jkobler/tricorder-GUI/resources/3D Models/01. TOS Tricorder(Empty)-STL Files/C.jpg

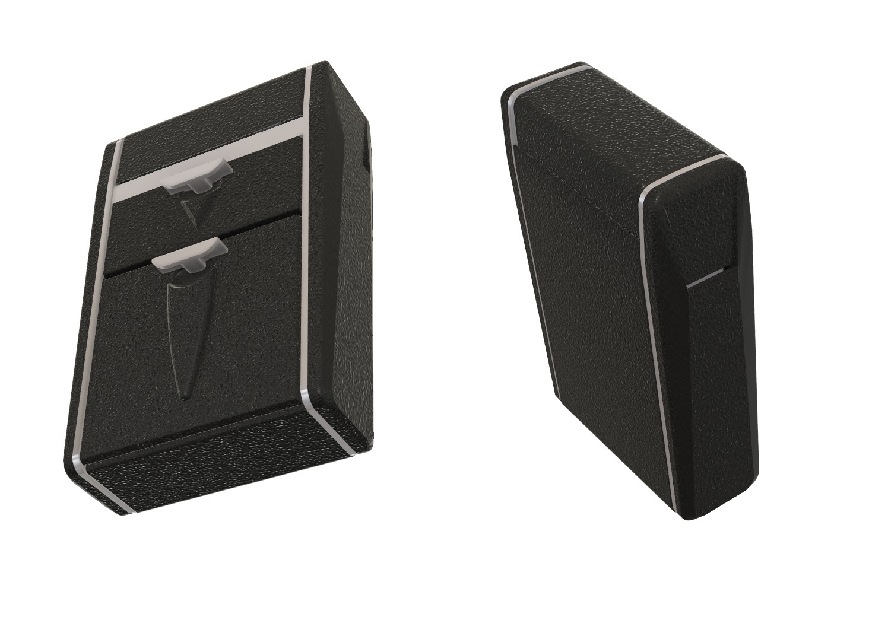
resources/3D Models/01. TOS Tricorder(Empty)-STL Files/C.jpg
