jkobler/tricorder-GUI/resources/3D Models/01. TOS Tricorder(Empty)-STL Files/L.jpg

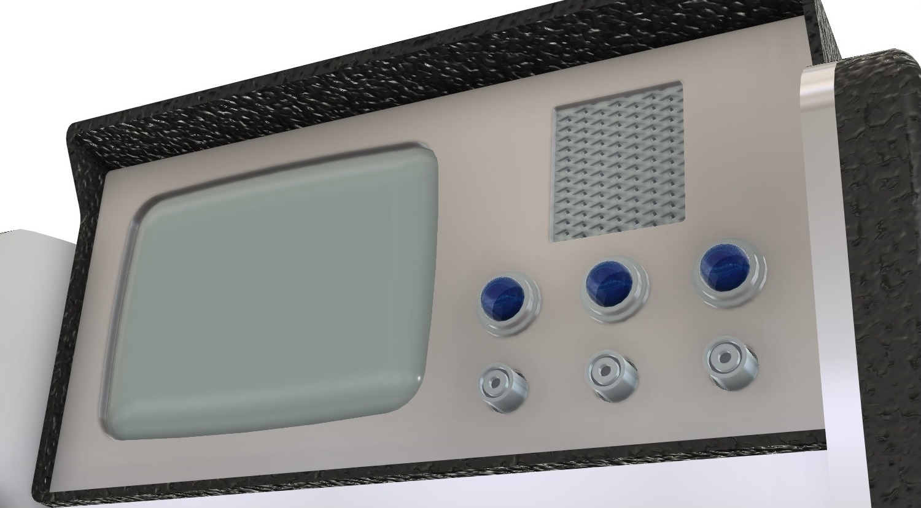
resources/3D Models/01. TOS Tricorder(Empty)-STL Files/L.jpg
