jkobler/tricorder-GUI/resources/3D Models/01. TOS Tricorder(Empty)-STL Files/M.jpg

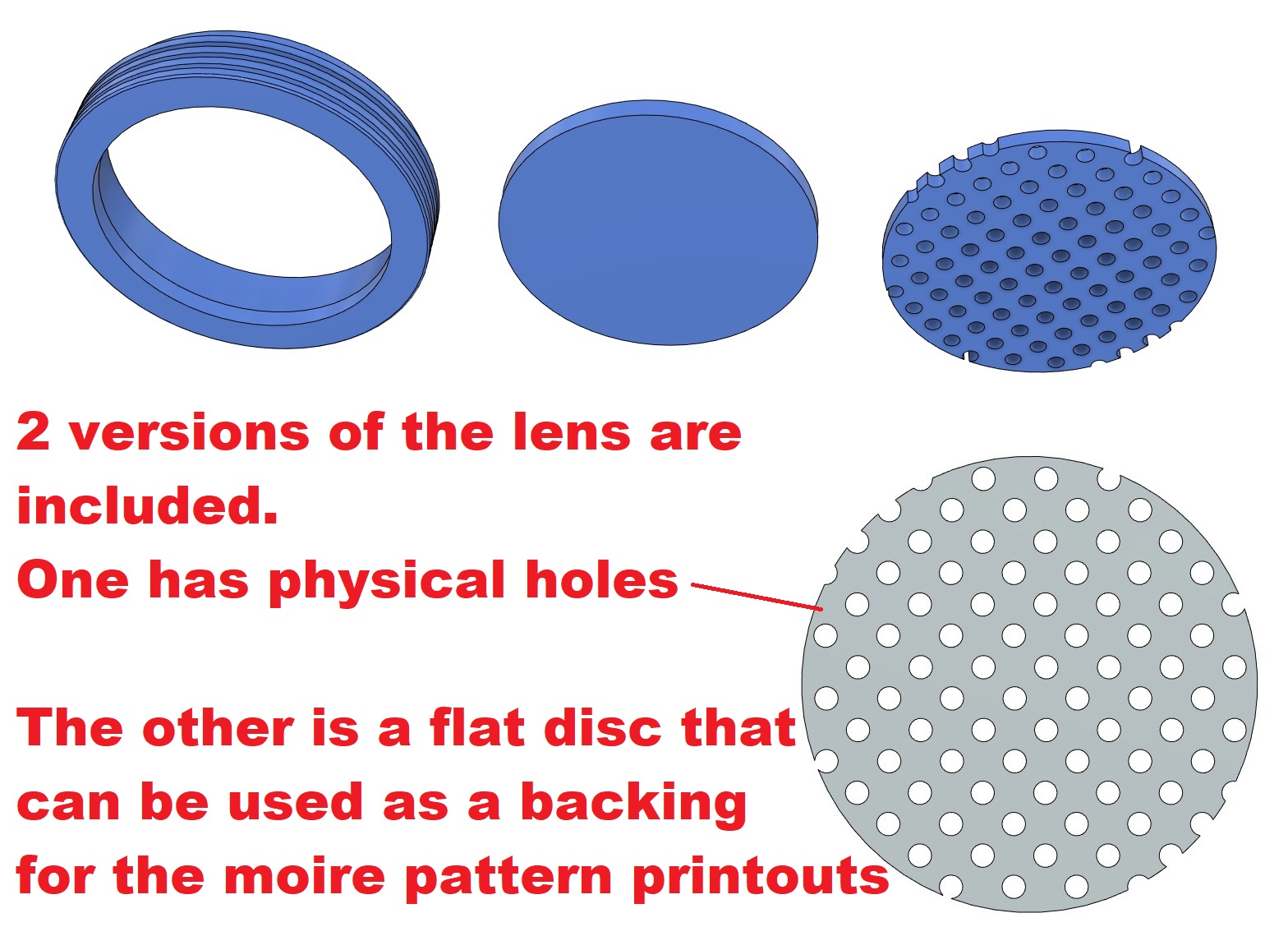
resources/3D Models/01. TOS Tricorder(Empty)-STL Files/M.jpg
