jkobler/tricorder-GUI/resources/3D Models/01. TOS Tricorder(Empty)-STL Files/Matts P1 - side view - internal sketch 1 - drawing 2.2.B-(C)Z.png

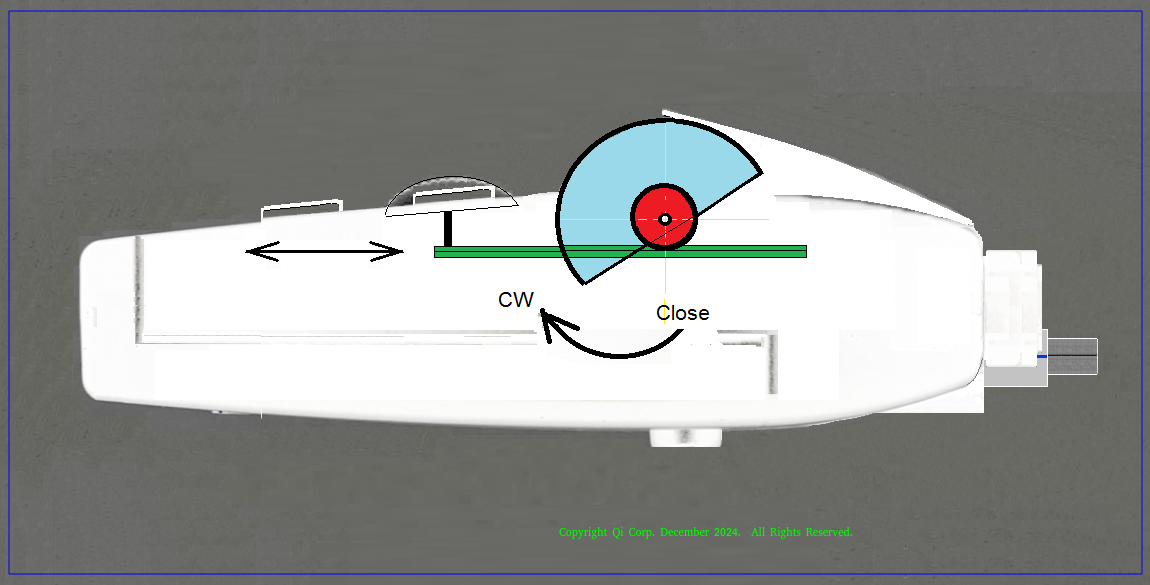
resources/3D Models/01. TOS Tricorder(Empty)-STL Files/Matts P1 - side view - internal sketch 1 - drawing 2.2.B-(C)Z.png
