jkobler/tricorder-GUI/resources/3D Models/01. TOS Tricorder(Empty)-STL Files/X.jpg

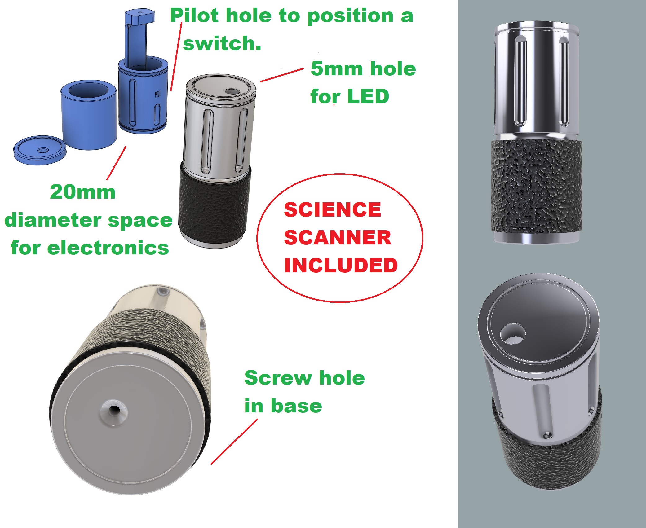
resources/3D Models/01. TOS Tricorder(Empty)-STL Files/X.jpg
