jkobler/tricorder-GUI/resources/images/2.0 TFT Display Block.JPG

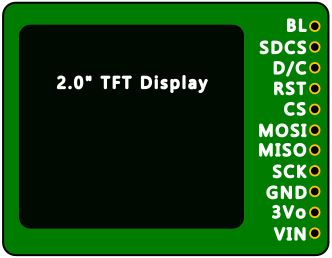
resources/images/2.0 TFT Display Block.JPG
