jkobler/tricorder-GUI/resources/images/Feather ESP32-S2 Block.JPG

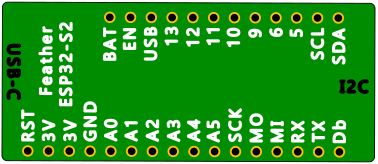
resources/images/Feather ESP32-S2 Block.JPG
