jkobler/tricorder-GUI/resources/images/Moire/Moire1200-BetaBottom.jpg

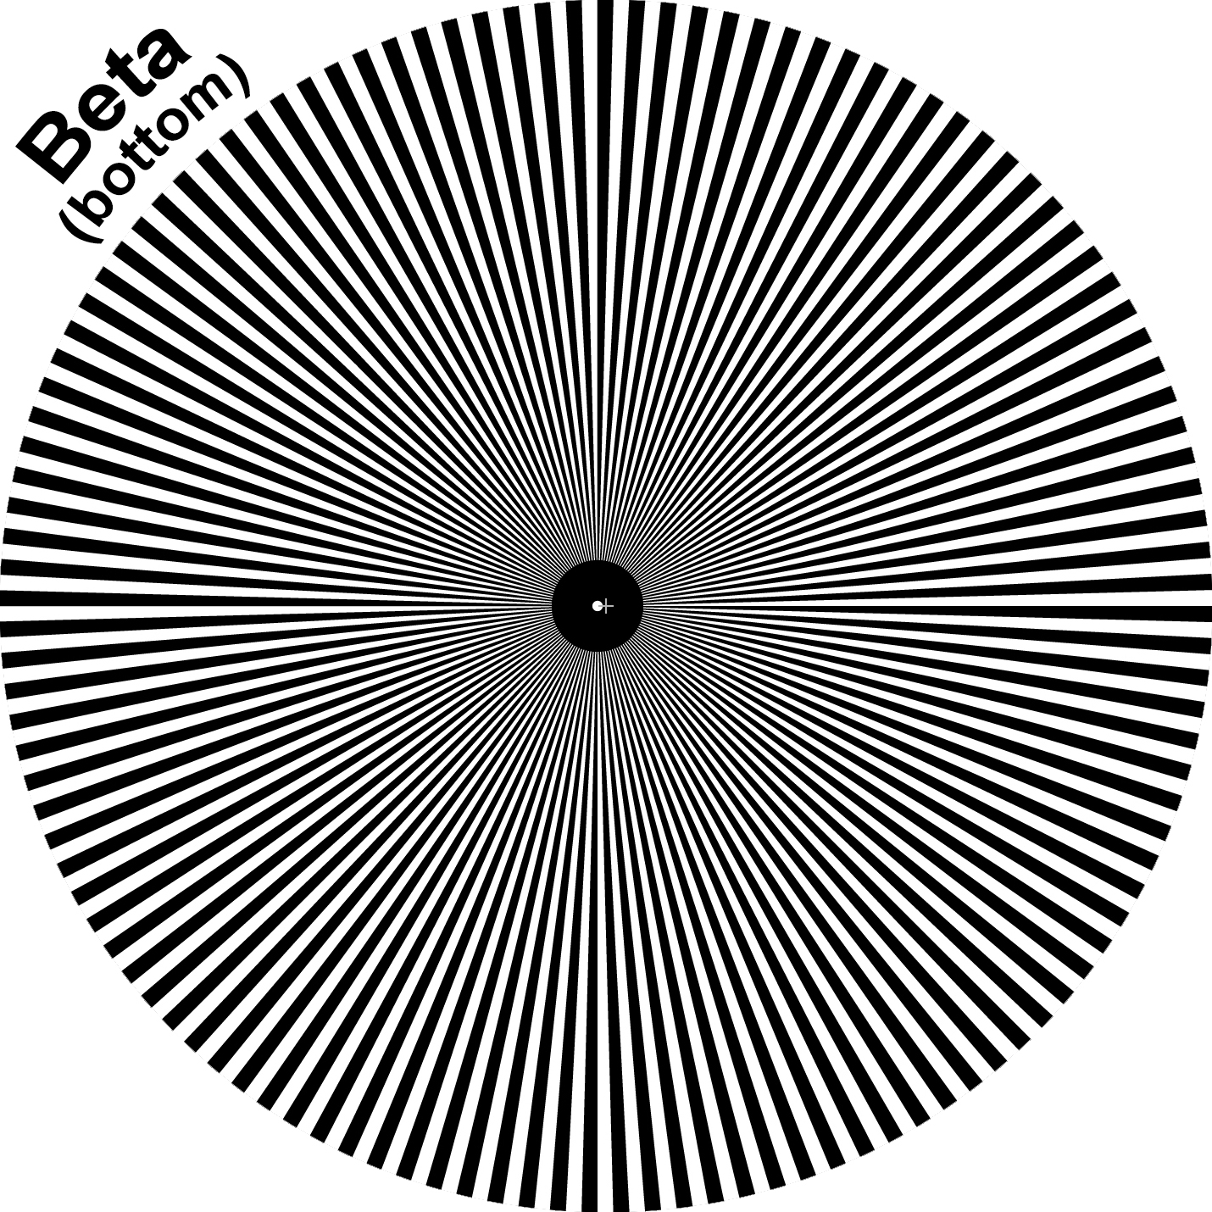
resources/images/Moire/Moire1200-BetaBottom.jpg
