jkobler/tricorder-GUI/resources/images/Moire/Moire1200-BetaTop.jpg

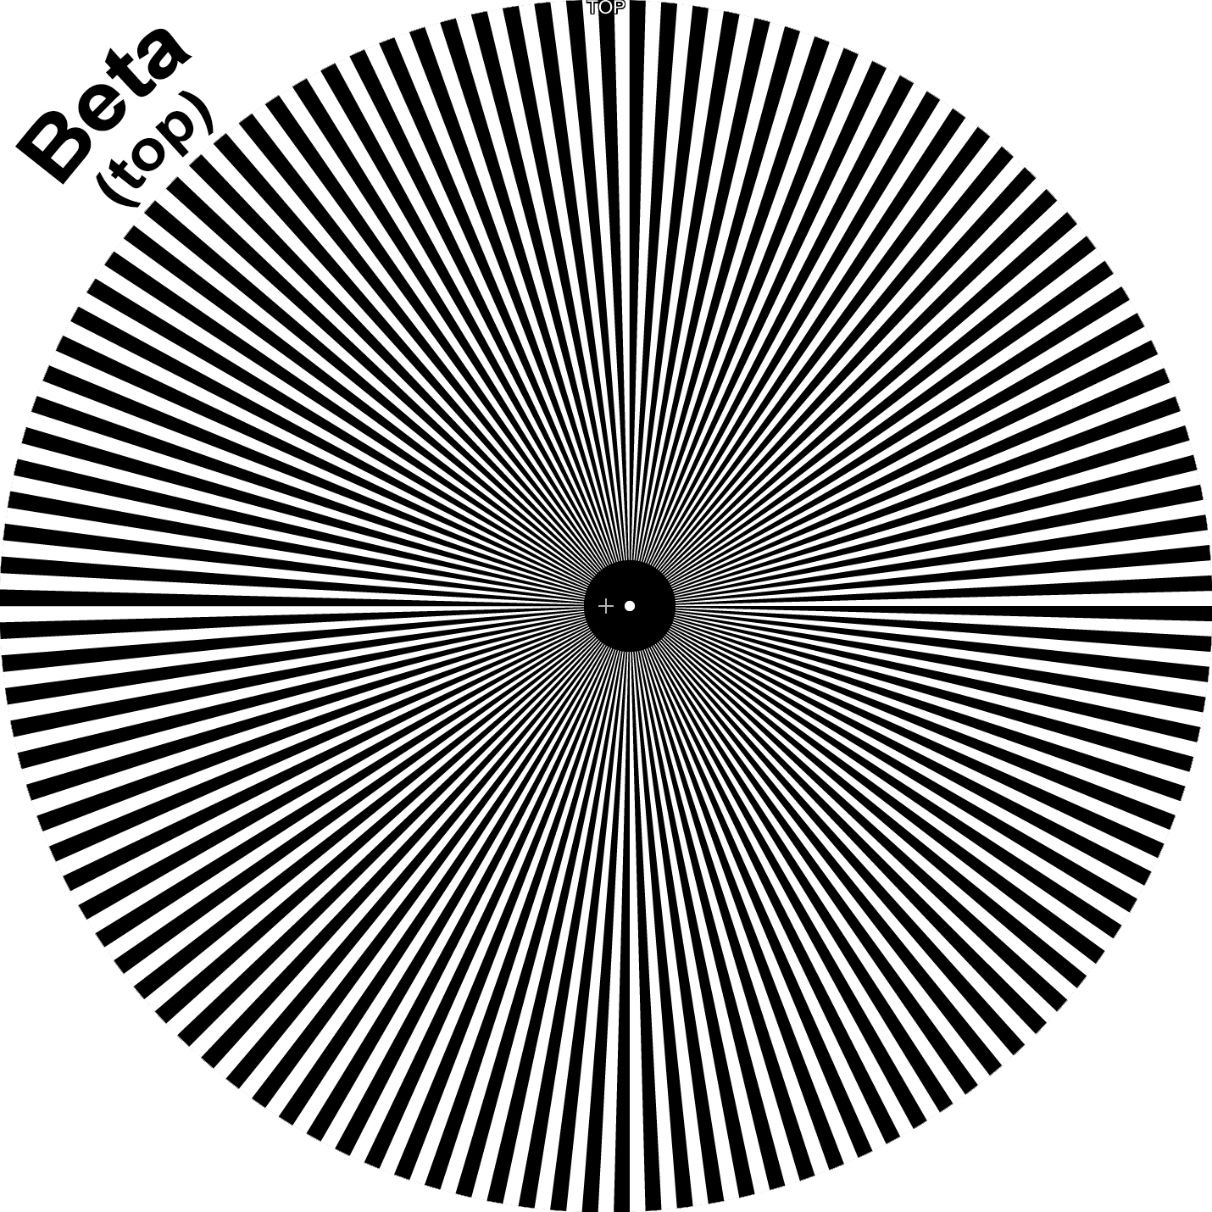
resources/images/Moire/Moire1200-BetaTop.jpg
