jkobler/tricorder-GUI/resources/images/reference photos/audio card hookups.JPG

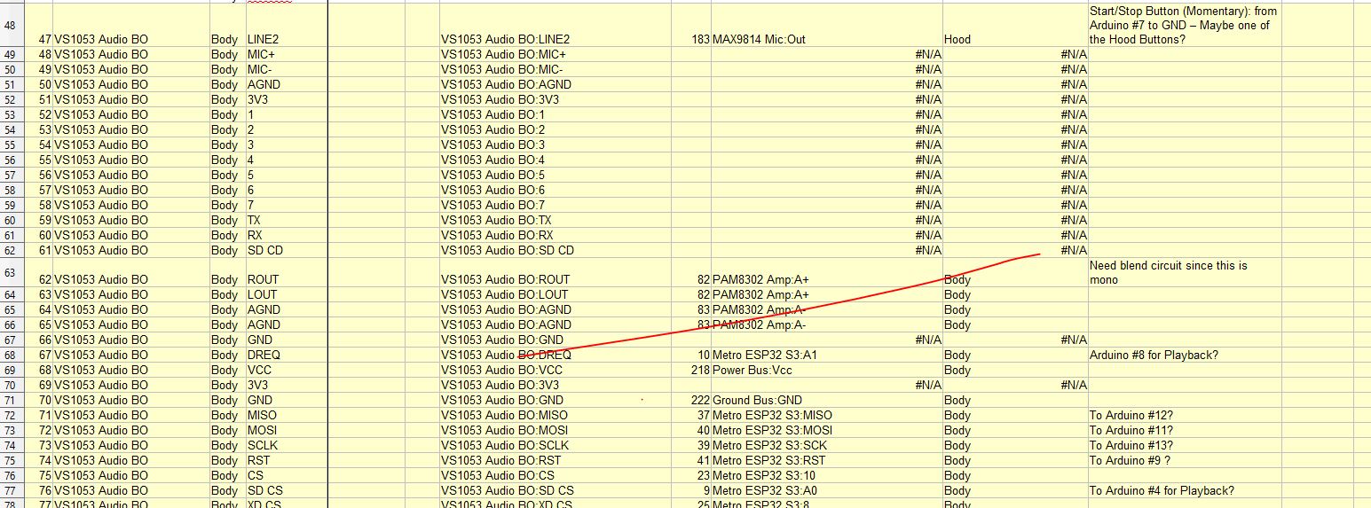
resources/images/reference photos/audio card hookups.JPG
