jkobler/tricorder-GUI/resources/images/reference photos/hero/18.jpg

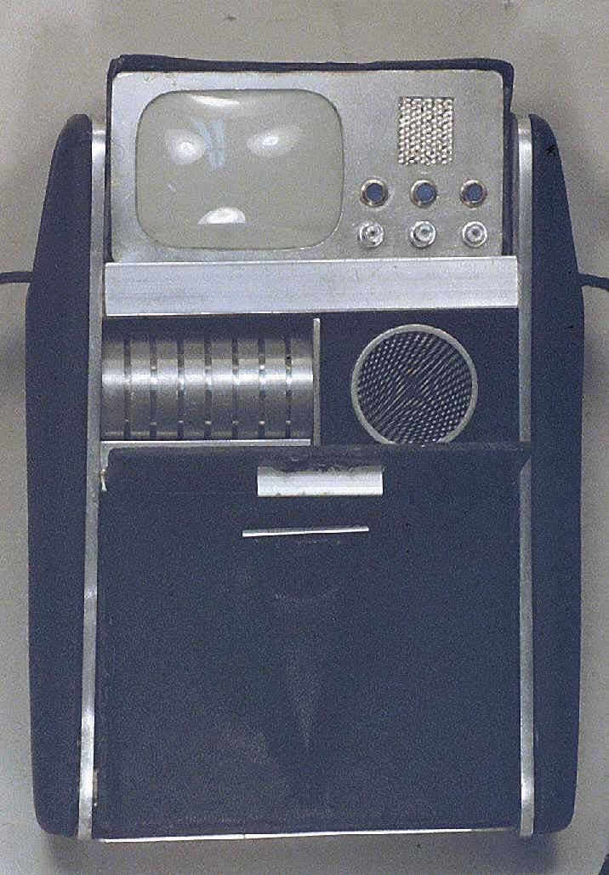
resources/images/reference photos/hero/18.jpg
