jkobler/tricorder-GUI/resources/images/reference photos/hero/CTriBook.jpg

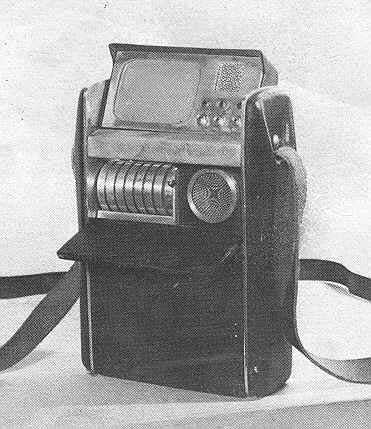
resources/images/reference photos/hero/CTriBook.jpg
