jkobler/tricorder-GUI/resources/images/reference photos/hero/CTriFulBot.jpg

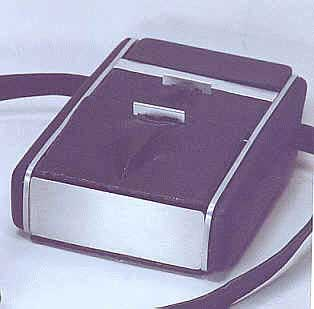
resources/images/reference photos/hero/CTriFulBot.jpg
