jkobler/tricorder-GUI/resources/images/reference photos/hero/Jein CU1 (1).jpg

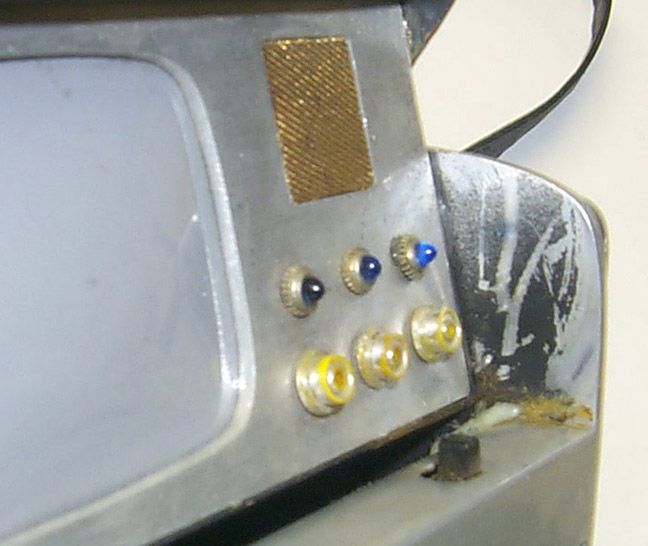
resources/images/reference photos/hero/Jein CU1 (1).jpg
