jkobler/tricorder-GUI/resources/images/reference photos/hero/JewelTricorderX2.jpg

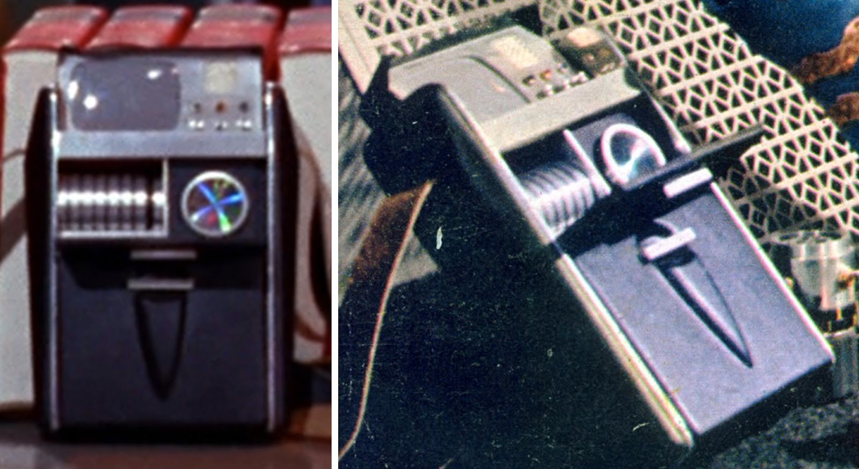
resources/images/reference photos/hero/JewelTricorderX2.jpg
