jkobler/tricorder-GUI/resources/images/reference photos/hero/lf (1).jpg

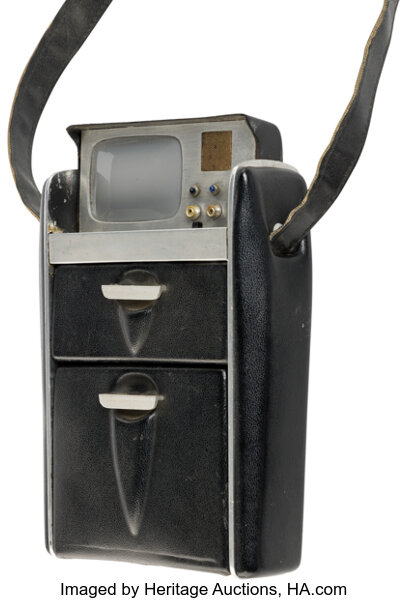
resources/images/reference photos/hero/lf (1).jpg
