jkobler/tricorder-GUI/resources/images/reference photos/hero/lf (2).jpg

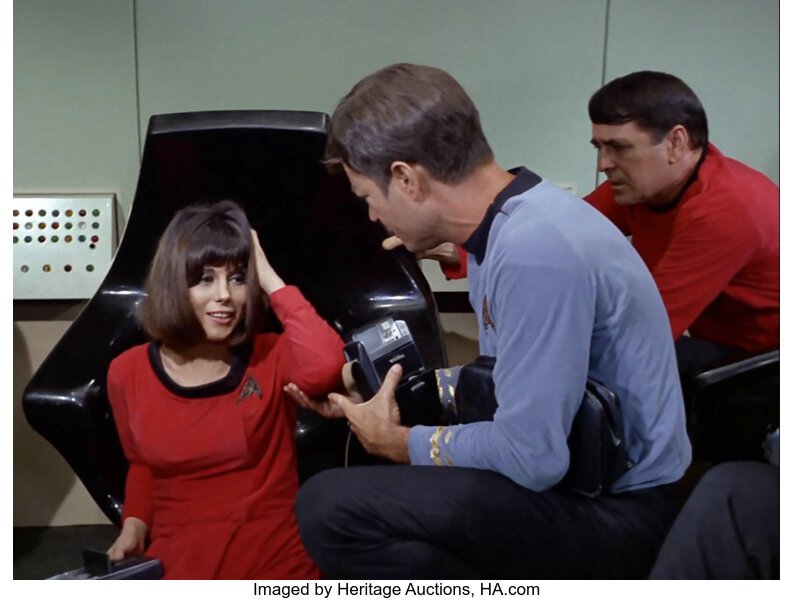
resources/images/reference photos/hero/lf (2).jpg
