jkobler/tricorder-GUI/resources/images/reference photos/hero/lf (3).jpg

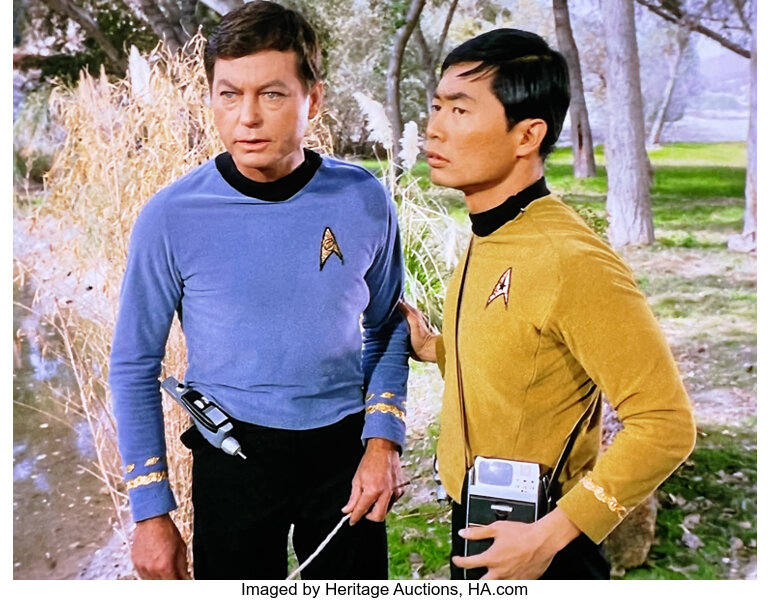
resources/images/reference photos/hero/lf (3).jpg
