jkobler/tricorder-GUI/resources/images/reference photos/hero/lf (4).jpg

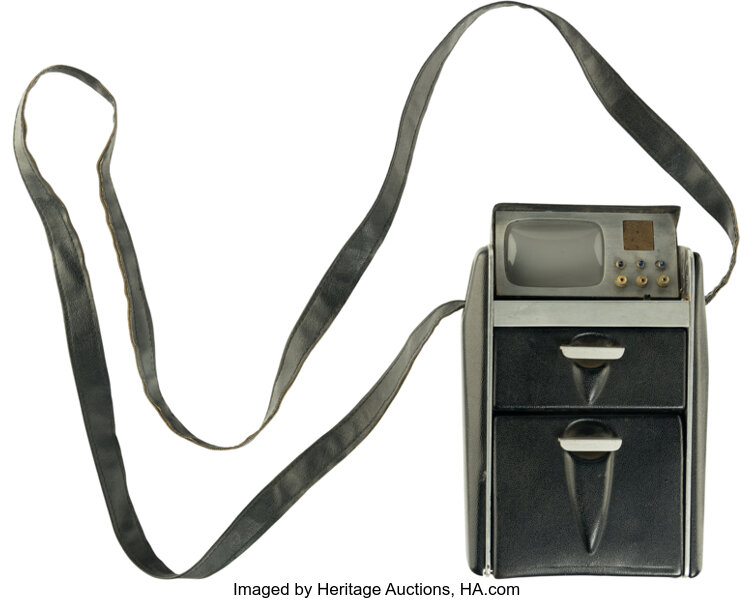
resources/images/reference photos/hero/lf (4).jpg
