jkobler/tricorder-GUI/resources/images/reference photos/hero/lf (5).jpg

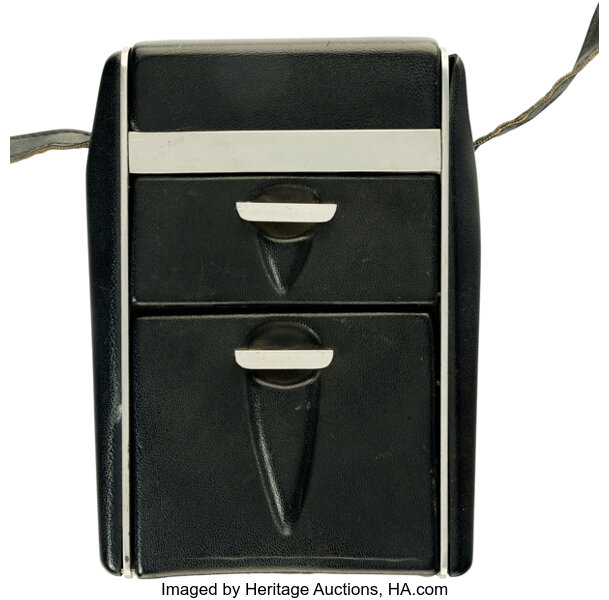
resources/images/reference photos/hero/lf (5).jpg
