jkobler/tricorder-GUI/resources/images/reference photos/hero/lf (6).jpg

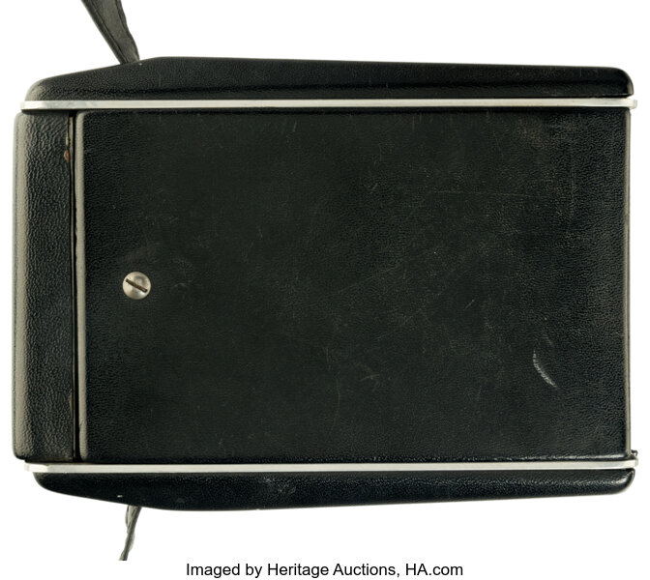
resources/images/reference photos/hero/lf (6).jpg
