jkobler/tricorder-GUI/resources/images/reference photos/hero/lf (7).jpg

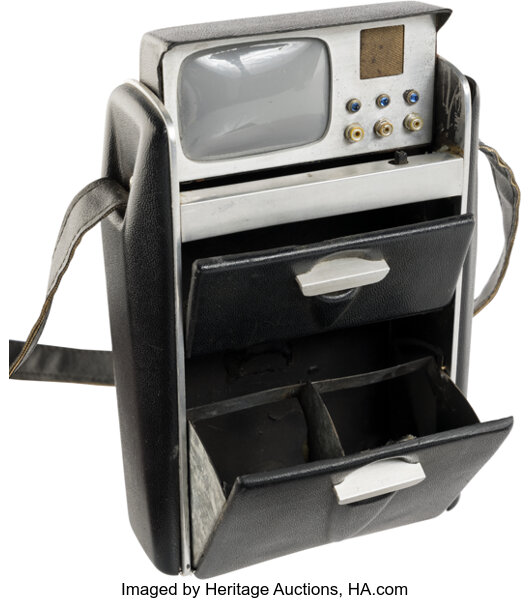
resources/images/reference photos/hero/lf (7).jpg
