jkobler/tricorder-GUI/resources/images/reference photos/hero/lf.jpg

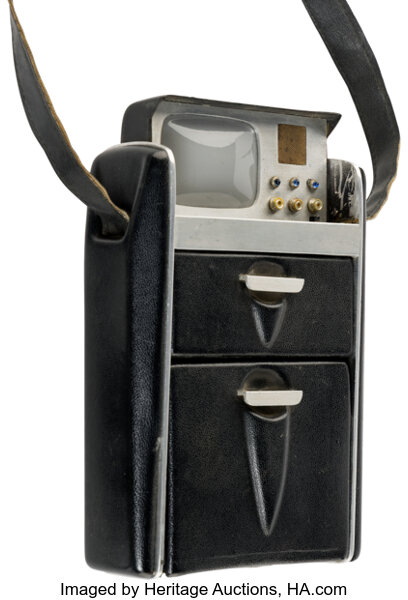
resources/images/reference photos/hero/lf.jpg
