jkobler/tricorder-GUI/resources/images/reference photos/hero/MoireTricCompare.jpg

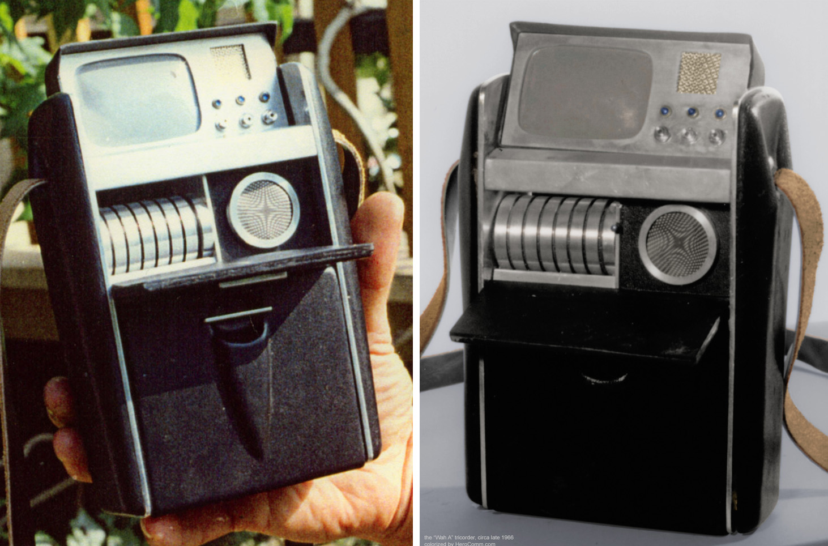
resources/images/reference photos/hero/MoireTricCompare.jpg
