jkobler/tricorder-GUI/resources/images/reference photos/hero/Starfleet_tricorder%2C_2260s.webp

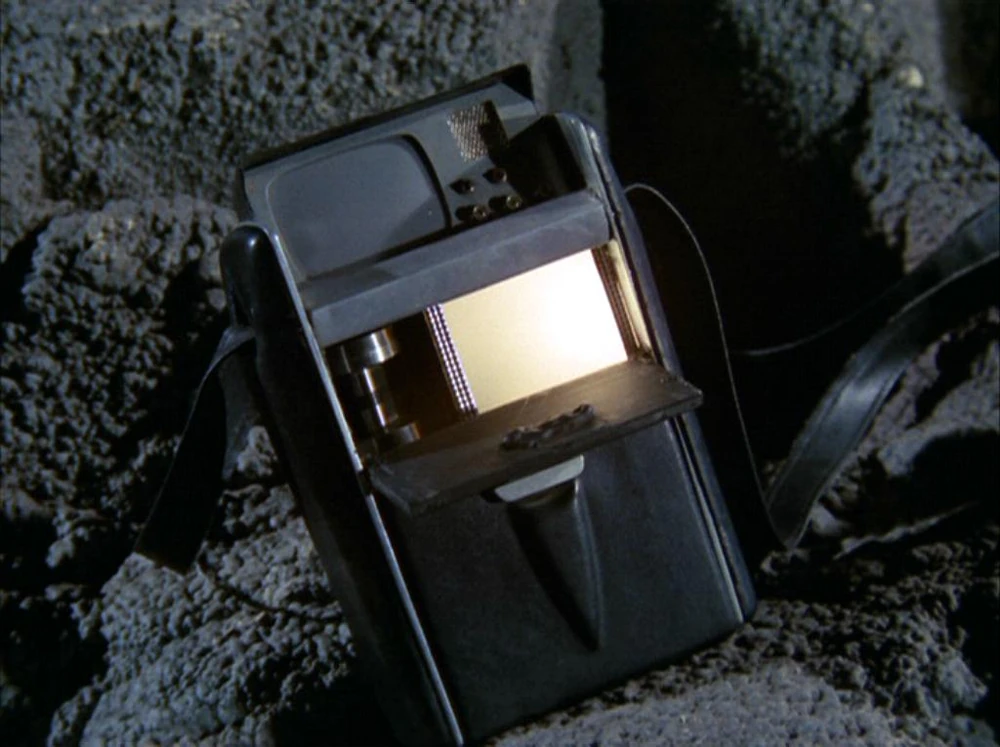
resources/images/reference photos/hero/Starfleet_tricorder%2C_2260s.webp
