jkobler/tricorder-GUI/resources/images/reference photos/hero/tricorder11.jpg

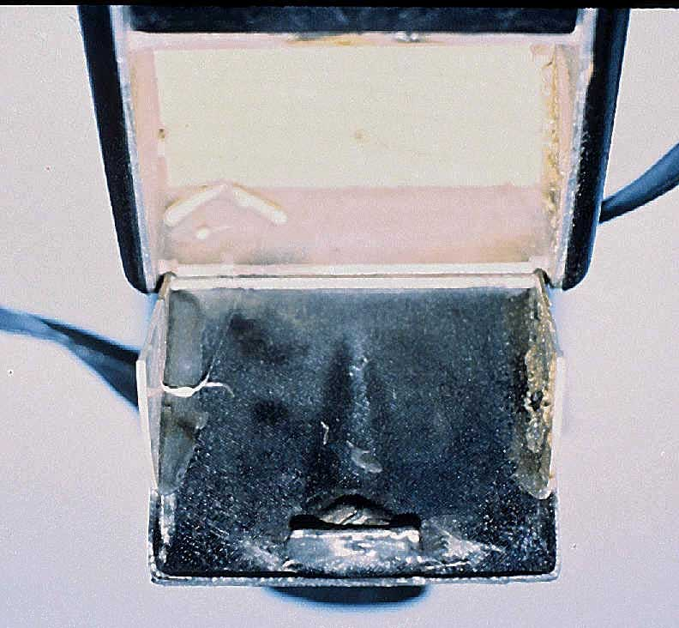
resources/images/reference photos/hero/tricorder11.jpg
