jkobler/tricorder-GUI/resources/images/reference photos/hero/tricorder13.jpg

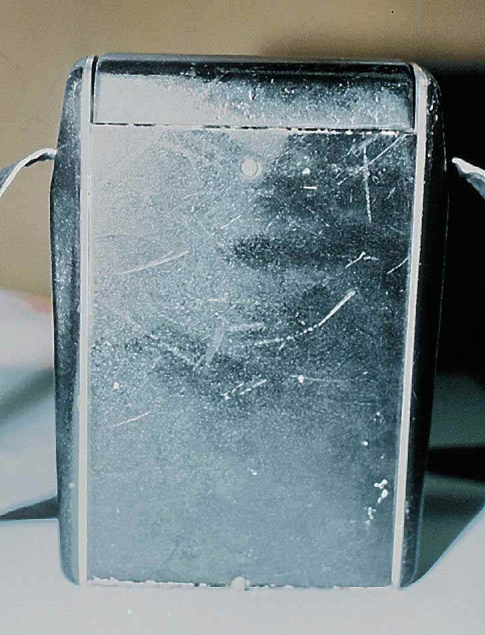
resources/images/reference photos/hero/tricorder13.jpg
