jkobler/tricorder-GUI/resources/images/reference photos/hero/tricorder15.jpg

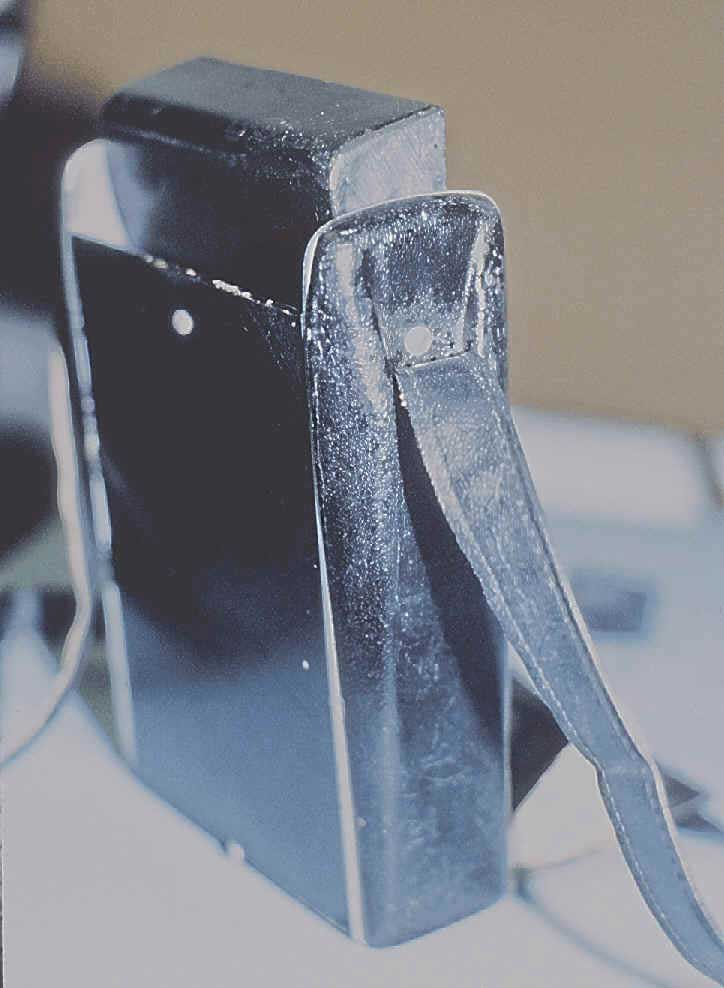
resources/images/reference photos/hero/tricorder15.jpg
