jkobler/tricorder-GUI/resources/images/reference photos/hero/tricorder17.jpg

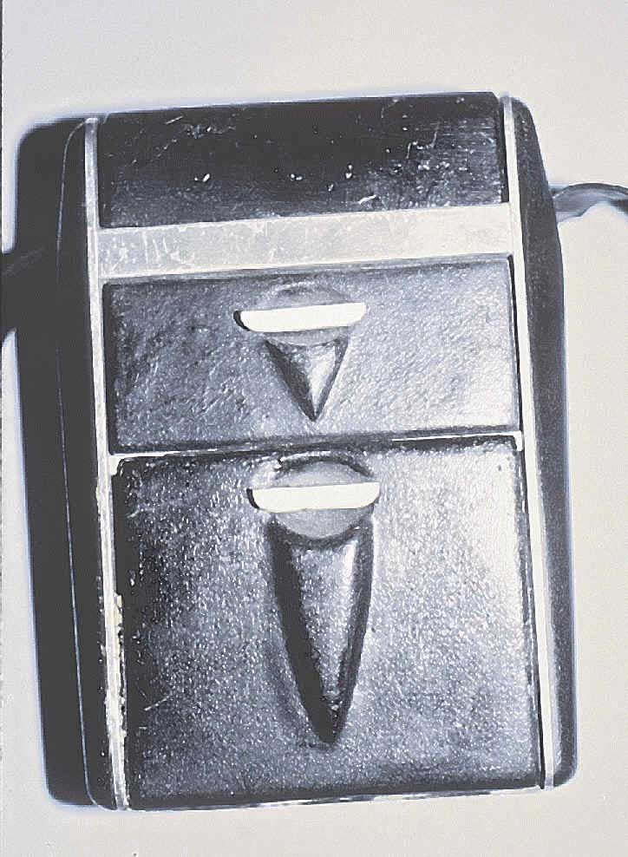
resources/images/reference photos/hero/tricorder17.jpg
