jkobler/tricorder-GUI/resources/images/reference photos/hero/tricorderCTriSideFront.jpg

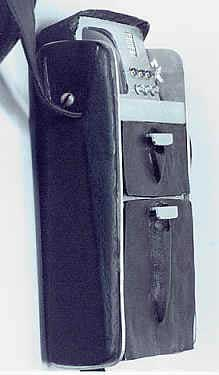
resources/images/reference photos/hero/tricorderCTriSideFront.jpg
