jkobler/tricorder-GUI/resources/images/reference photos/hero/tricorderCTriTVPix1.jpg

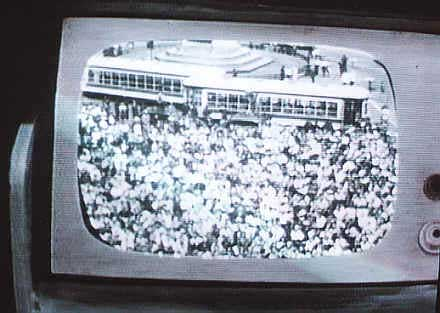
resources/images/reference photos/hero/tricorderCTriTVPix1.jpg
