jkobler/tricorder-GUI/resources/images/reference photos/hero/tricorderCTriTVPix2.jpg

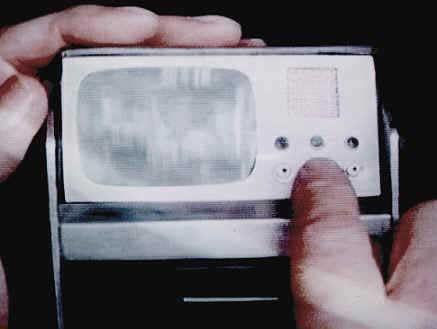
resources/images/reference photos/hero/tricorderCTriTVPix2.jpg
