jkobler/tricorder-GUI/resources/images/reference photos/hero/TricorderHeroCallouts.jpg

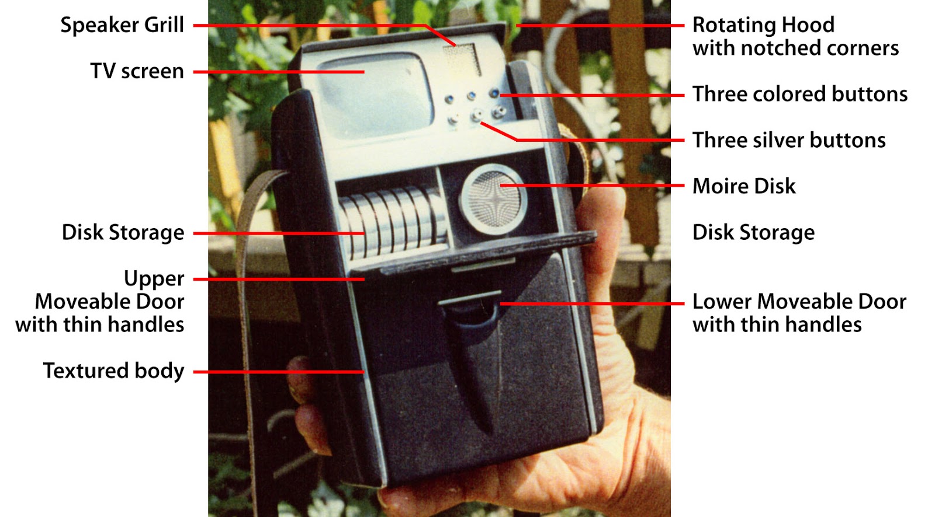
resources/images/reference photos/hero/TricorderHeroCallouts.jpg
