jkobler/tricorder-GUI/resources/images/reference photos/hero/TricorderReceipt.jpg

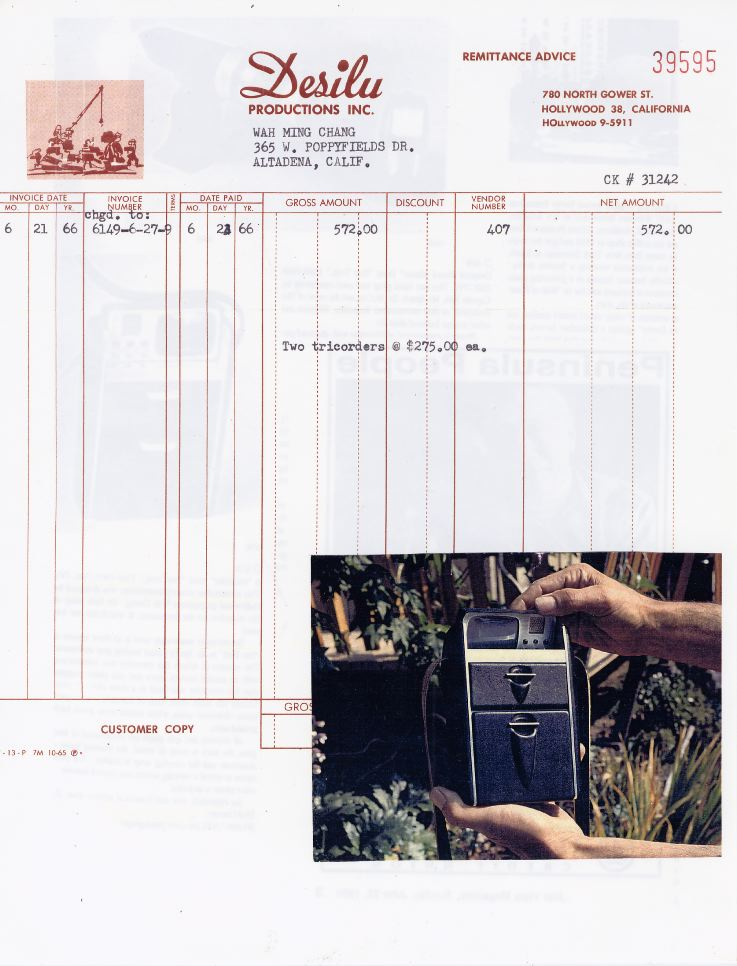
resources/images/reference photos/hero/TricorderReceipt.jpg
