jkobler/tricorder-GUI/resources/images/reference photos/hero/tricorderTrainWheels.jpg

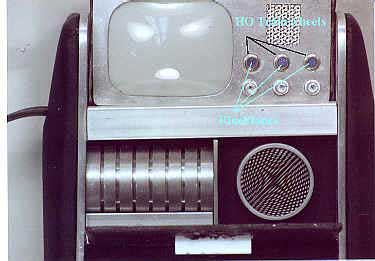
resources/images/reference photos/hero/tricorderTrainWheels.jpg
