jkobler/tricorder-GUI/resources/images/reference photos/hero/uss-enterprise-equipment-pack-sheet-11.jpg

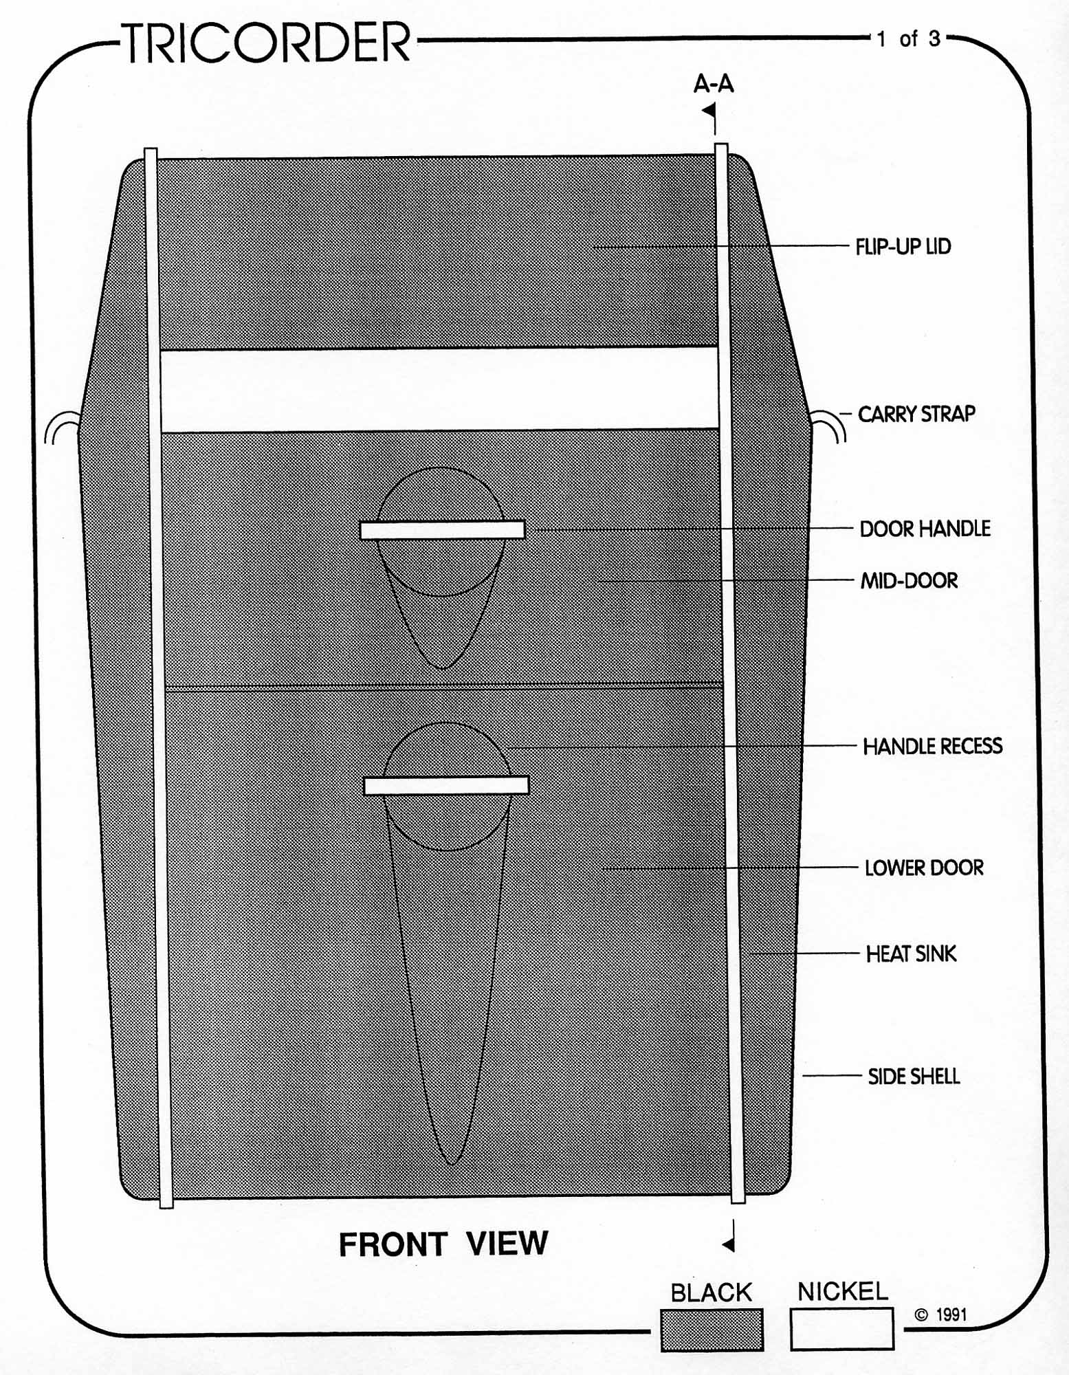
resources/images/reference photos/hero/uss-enterprise-equipment-pack-sheet-11.jpg
