jkobler/tricorder-GUI/resources/images/reference photos/hero/uss-enterprise-equipment-pack-sheet-12.jpg

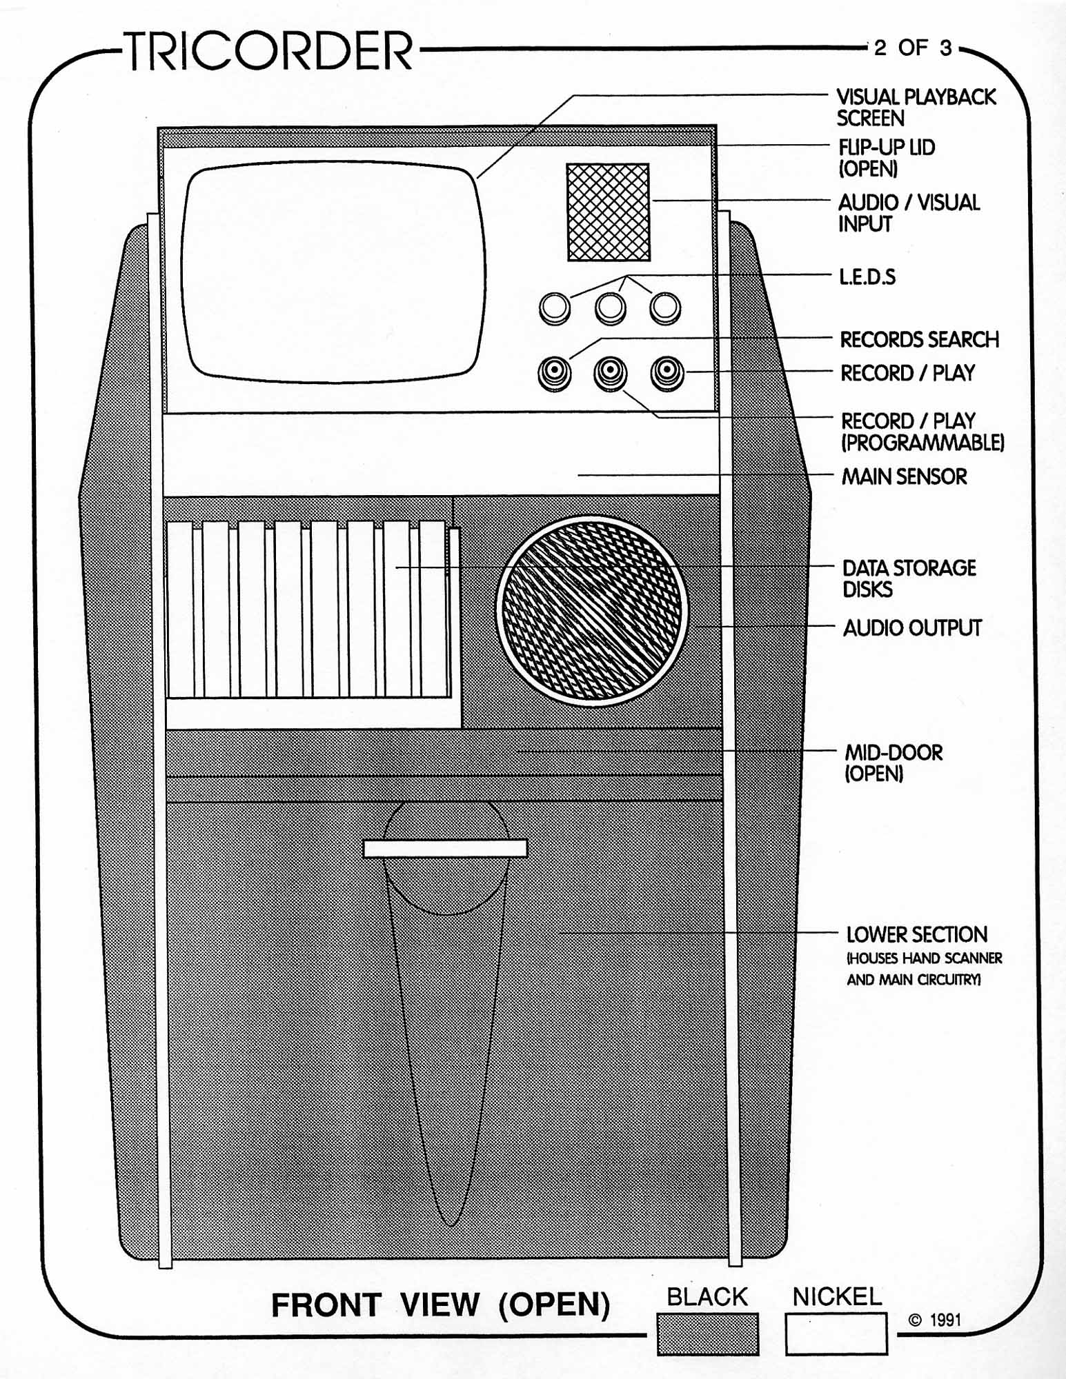
resources/images/reference photos/hero/uss-enterprise-equipment-pack-sheet-12.jpg
