jkobler/tricorder-GUI/resources/images/reference photos/hero/wah-chang-built-hero-starfleet-tricorder-from-star-trek--the-original-series_heritage_auctions-7252f1523d0a9d30684ac45ed7cd6dd10a9a74f2-s800-c85.webp

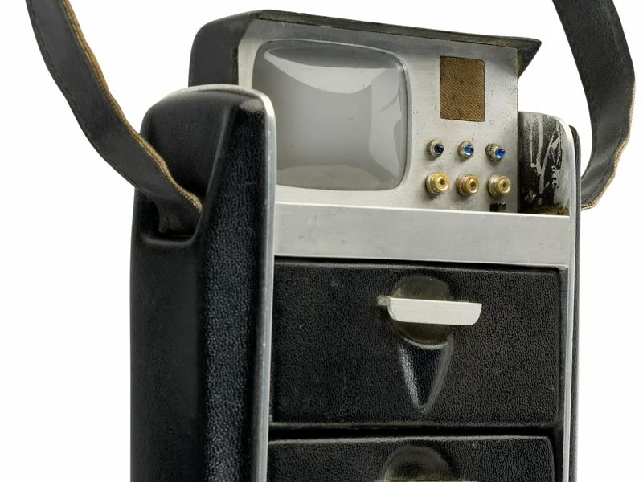
resources/images/reference photos/hero/wah-chang-built-hero-starfleet-tricorder-from-star-trek--the-original-series_heritage_auctions-7252f1523d0a9d30684ac45ed7cd6dd10a9a74f2-s800-c85.webp
