jkobler/tricorder-GUI/resources/images/reference photos/hero/Wahx2.jpg

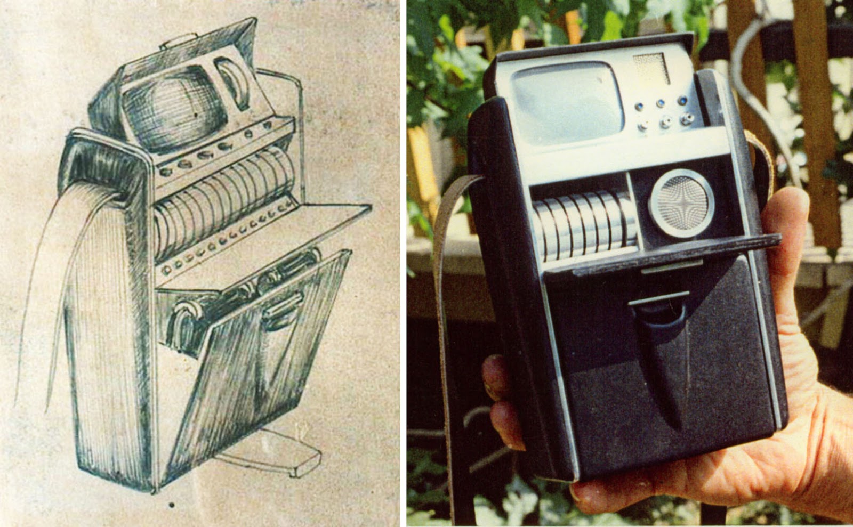
resources/images/reference photos/hero/Wahx2.jpg
