jkobler/tricorder-GUI/resources/images/reference photos/layout/240x320 2.2 inch TFT Screen.JPG

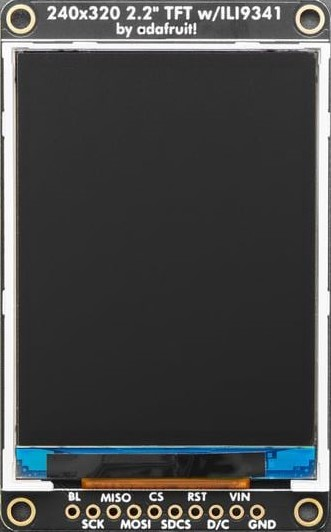
resources/images/reference photos/layout/240x320 2.2 inch TFT Screen.JPG
