jkobler/tricorder-GUI/resources/images/reference photos/layout/Tricorder body-Back.JPG

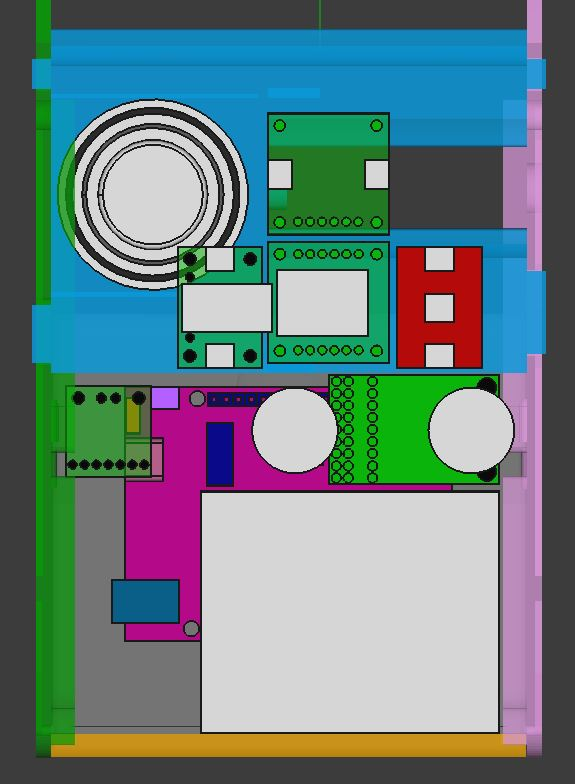
resources/images/reference photos/layout/Tricorder body-Back.JPG
