jkobler/tricorder-GUI/resources/images/reference photos/layout/Tricorder body-Front.JPG

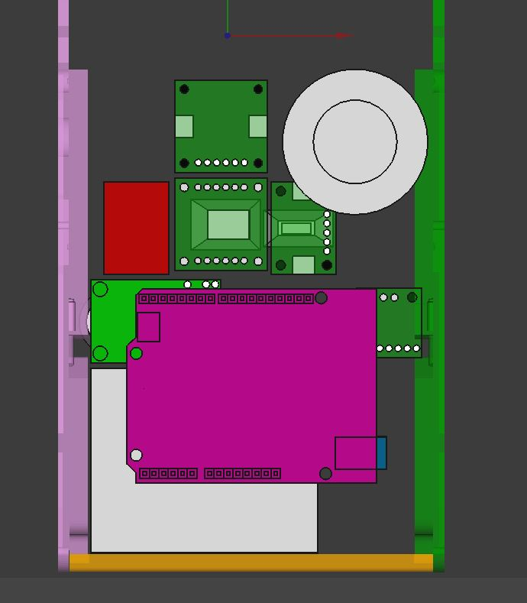
resources/images/reference photos/layout/Tricorder body-Front.JPG
