jkobler/tricorder-GUI/resources/images/reference photos/layout/Tricorder hood-Back.JPG

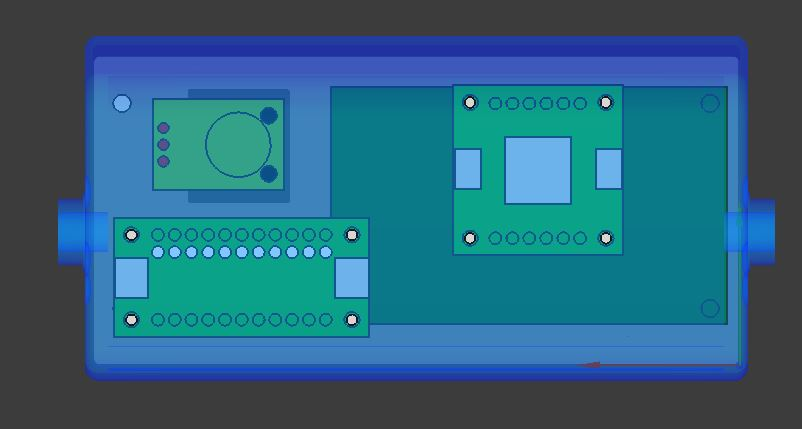
resources/images/reference photos/layout/Tricorder hood-Back.JPG
