jkobler/tricorder-GUI/resources/images/reference photos/layout/Tricorder hood-Bottom.JPG

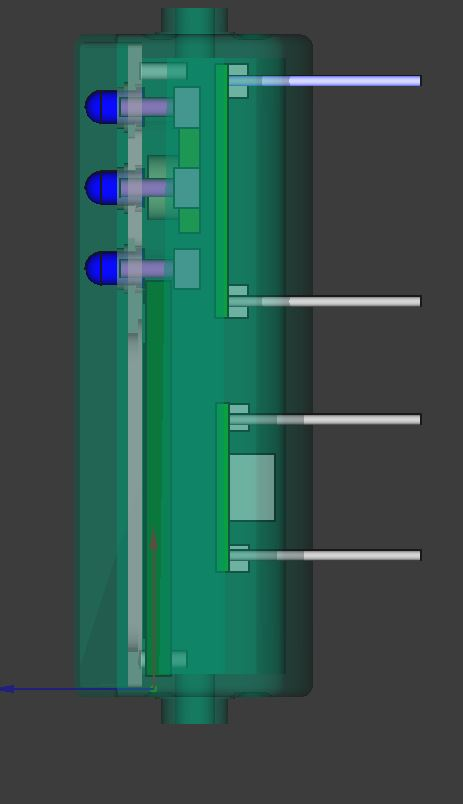
resources/images/reference photos/layout/Tricorder hood-Bottom.JPG
