jkobler/tricorder-GUI/resources/images/reference photos/layout/Tricorder hood-Front.JPG

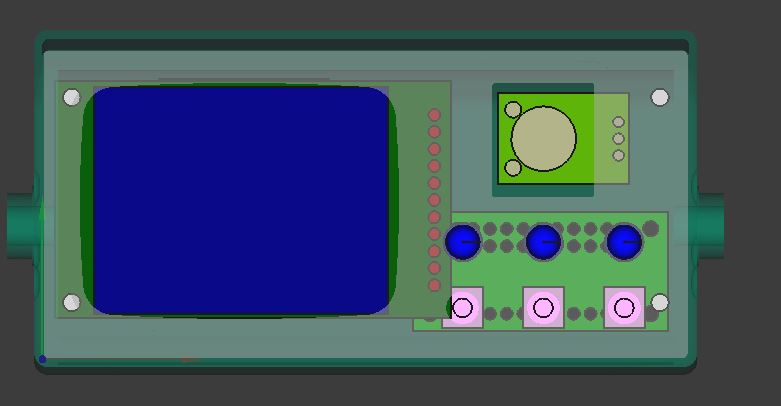
resources/images/reference photos/layout/Tricorder hood-Front.JPG
