jkobler/tricorder-GUI/resources/images/reference photos/layout/Tricorder hood-Left.JPG

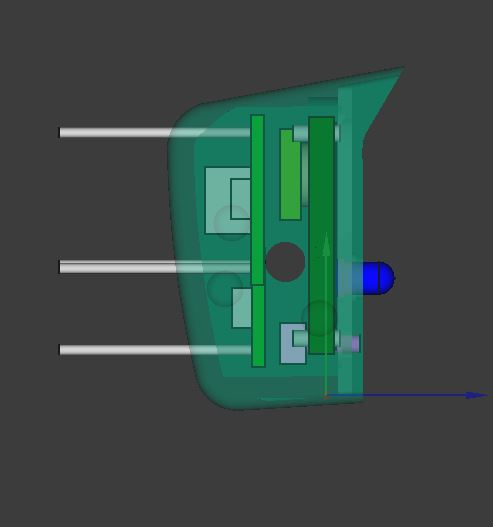
resources/images/reference photos/layout/Tricorder hood-Left.JPG
