jkobler/tricorder-GUI/resources/images/Seesaw Encoder Block.JPG

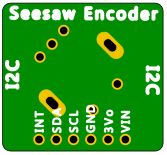
resources/images/Seesaw Encoder Block.JPG
