jkobler/tricorder-GUI/resources/images/starfleet_TOS-2.gif

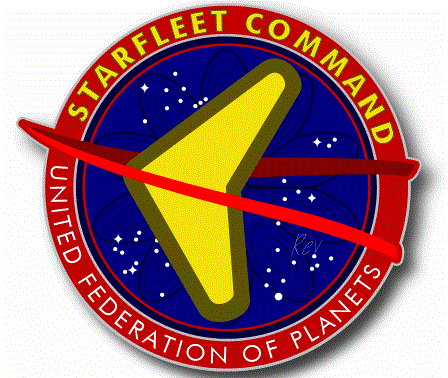
resources/images/starfleet_TOS-2.gif
