jkobler/tricorder-GUI/resources/images/Switches Block.JPG

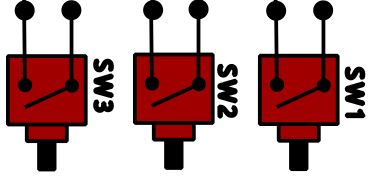
resources/images/Switches Block.JPG
