jkobler/tricorder-GUI/resources/images/Tricorder Screen 1.bmp

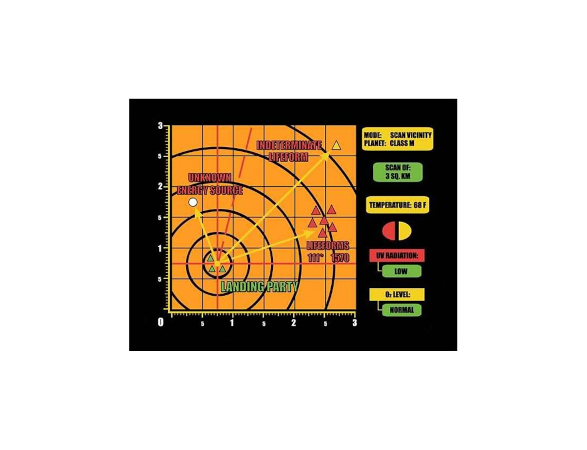
resources/images/Tricorder Screen 1.bmp
