jkobler/tricorder-GUI/resources/3D Models/Tricorder Test Stands-Hood buttons and LEDs.stl

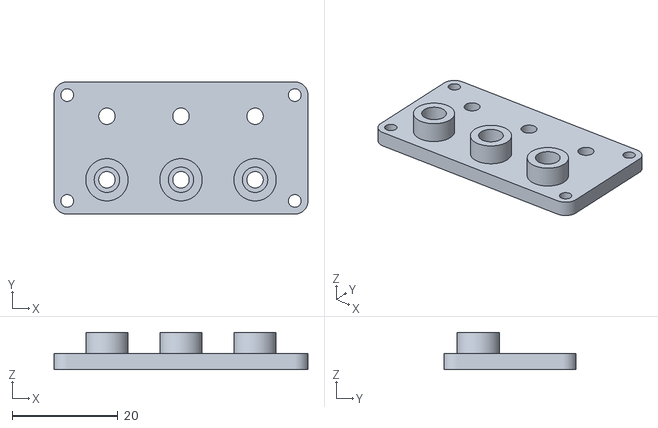
[picture p87: CAD file, 2025-12-18]
resources/3D Models/Tricorder Test Stands-Hood buttons and LEDs.stl
48.0 x 25.0 x 7.00
