jkobler/tricorder-GUI/resources/3D Models/01. TOS Tricorder(Empty)-STL Files/TTA1-Lens frame panel.stl

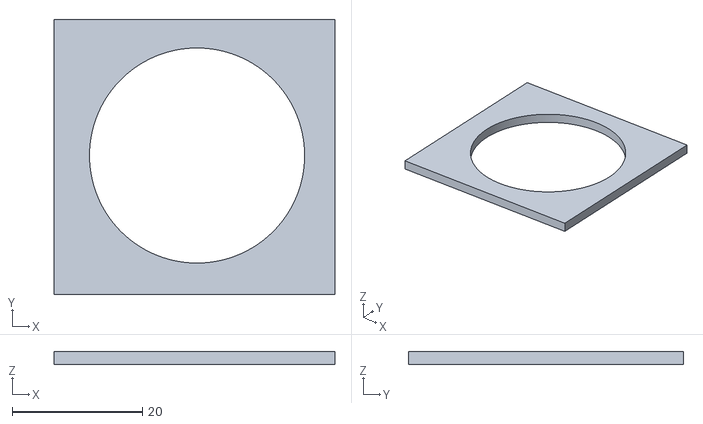
[picture p88: CAD file, 2025-12-18]
resources/3D Models/01. TOS Tricorder(Empty)-STL Files/TTA1-Lens frame panel.stl
43.2 x 42.3 x 2.00
