jkobler/tricorder-GUI/resources/3D Models/TRHV4-Hood Front Panel.3mf

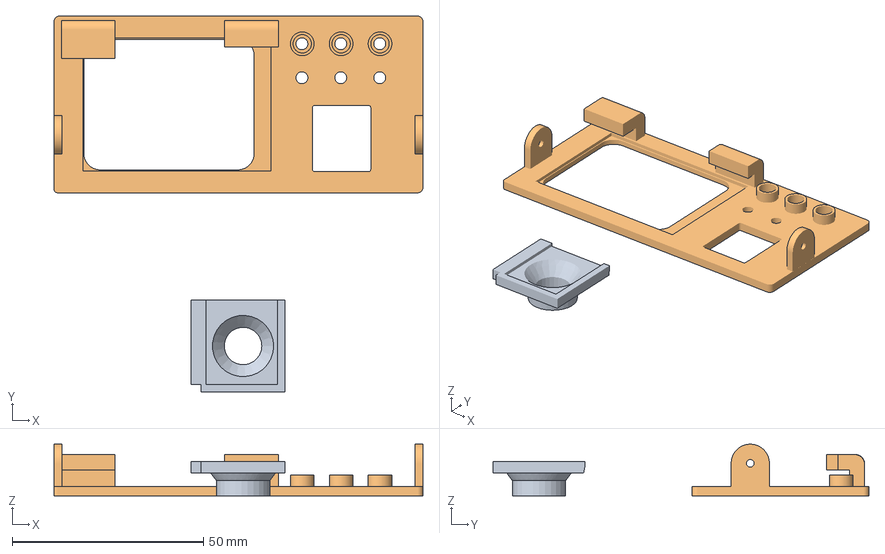
[picture p89: CAD file, 2025-12-18]
resources/3D Models/TRHV4-Hood Front Panel.3mf
96.4 x 98.2 x 13.5 mm
TRHV4-Hood Mic Bezel.stl
TRHV4-Hood Front Panel.stl
