jkobler/tricorder-GUI/resources/3D Models/01. TOS Tricorder(Empty)-STL Files/TTA1-Hood Facia Plate (with 5mm LED holes).stl

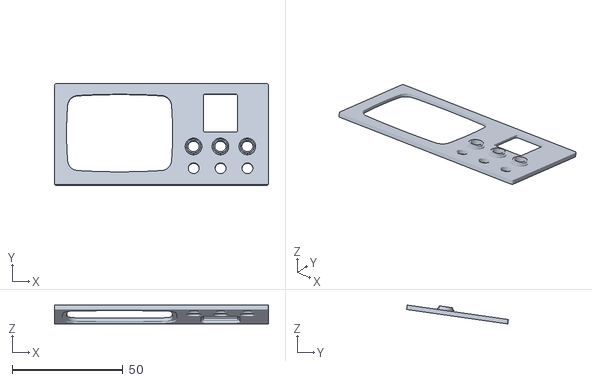
[picture p90: CAD file, 2025-12-18]
resources/3D Models/01. TOS Tricorder(Empty)-STL Files/TTA1-Hood Facia Plate (with 5mm LED holes).stl
96.4 x 45.8 x 8.49
