jkobler/tricorder-GUI/resources/3D Models/TTA1-Disk Encoder Casing Endcap.stl

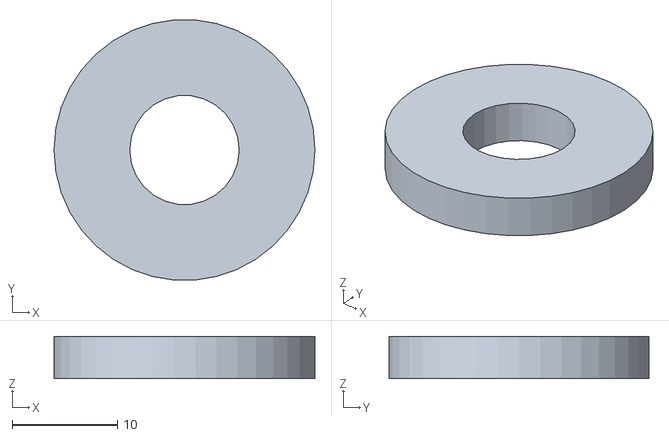
[picture p91: CAD file, 2025-12-18]
resources/3D Models/TTA1-Disk Encoder Casing Endcap.stl
24.8 x 24.7 x 4.00
