jkobler/tricorder-GUI/resources/3D Models/01. TOS Tricorder(Empty)-STL Files/TTA1-Screen.3mf

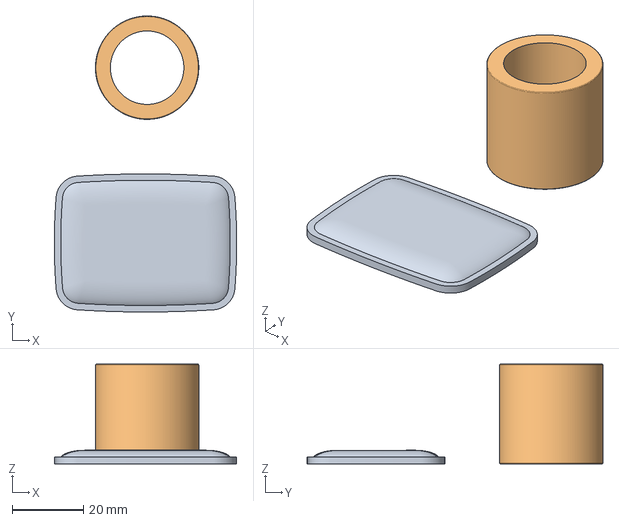
[picture p92: CAD file, 2025-12-18]
resources/3D Models/01. TOS Tricorder(Empty)-STL Files/TTA1-Screen.3mf
51.1 x 83.0 x 28.0 mm
TTA1-Screen.stl
TT-Science Scanner 2.stl
