jkobler/tricorder-GUI/resources/3D Models/TRHV4-LED Surround.stl

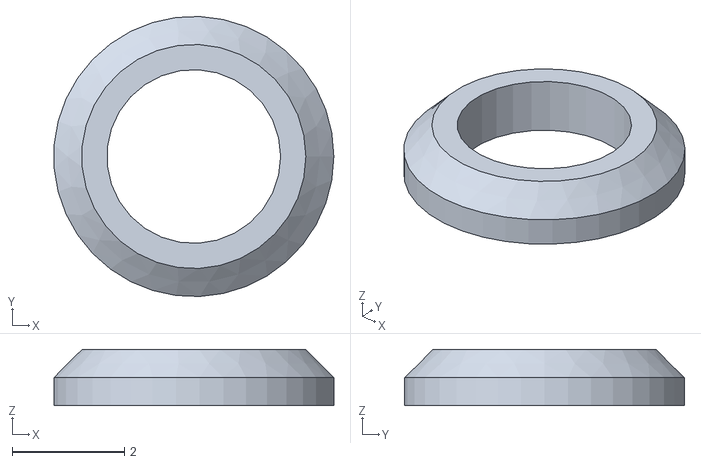
[picture p93: CAD file, 2025-12-18]
resources/3D Models/TRHV4-LED Surround.stl
4.99 x 5.00 x 1.00
