jkobler/tricorder-GUI/resources/3D Models/01. TOS Tricorder(Empty)-STL Files/TTA1-Lower Door (Handle B) (with magnet slot).stl

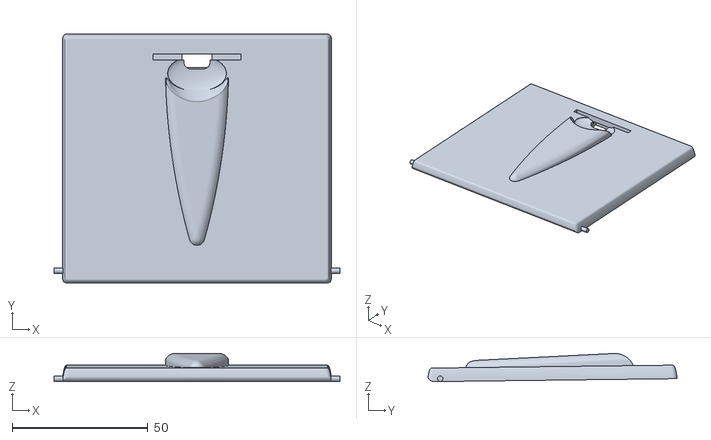
[picture p94: CAD file, 2025-12-18]
resources/3D Models/01. TOS Tricorder(Empty)-STL Files/TTA1-Lower Door (Handle B) (with magnet slot).stl
105.4 x 91.8 x 10.4
