jkobler/tricorder-GUI/resources/3D Models/Tricorder hood and facia plate V3.FCStd

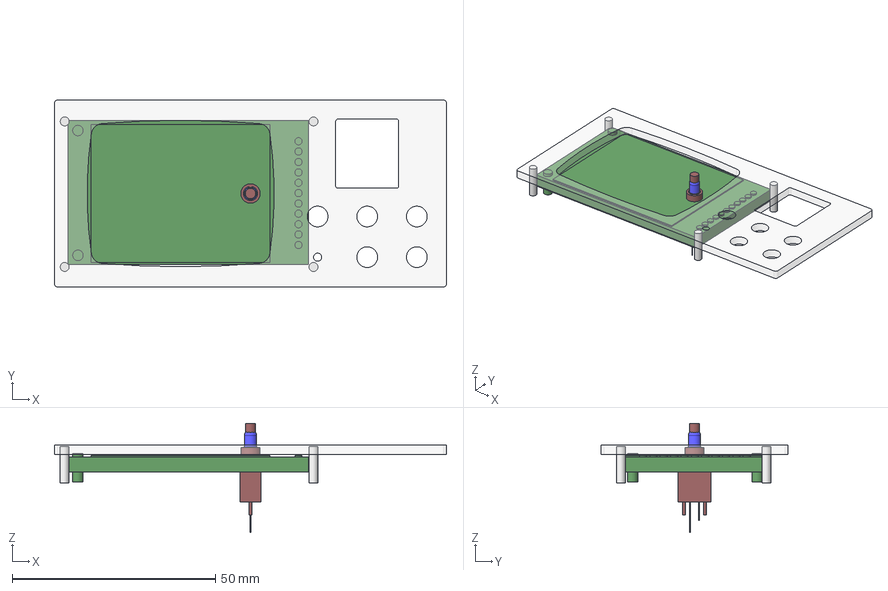
[picture p95: CAD file, 2025-12-18]
resources/3D Models/Tricorder hood and facia plate V3.FCStd
96.4 x 46.0 x 26.9 mm
Hood Facia Plate V3
mounting peg tft 001
mounting peg tft 002
mounting peg tft 003
mounting peg tft 004
3mm LED 001
Button 800AWSP9-001
Screen Assy tft 2.0
