jkobler/tricorder-GUI/resources/3D Models/01. TOS Tricorder(Empty)-STL Files/TTA1-Hood Mesh Square.stl

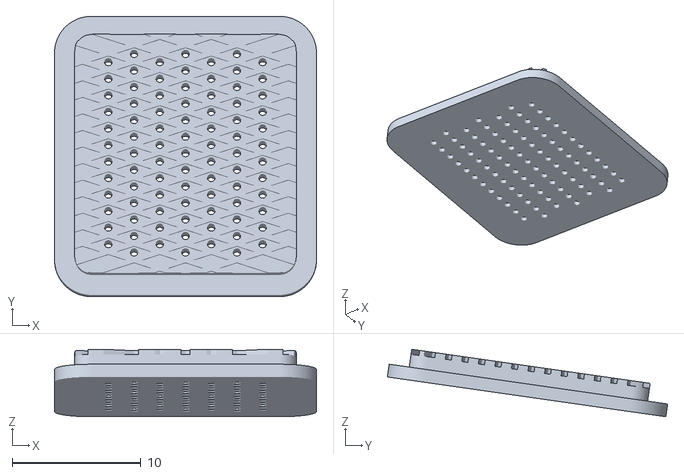
[picture p96: CAD file, 2025-12-18]
resources/3D Models/01. TOS Tricorder(Empty)-STL Files/TTA1-Hood Mesh Square.stl
20.4 x 21.8 x 5.25
