jkobler/tricorder-GUI/resources/3D Models/TRHV4-Hood Front Panel Udrillit.stl

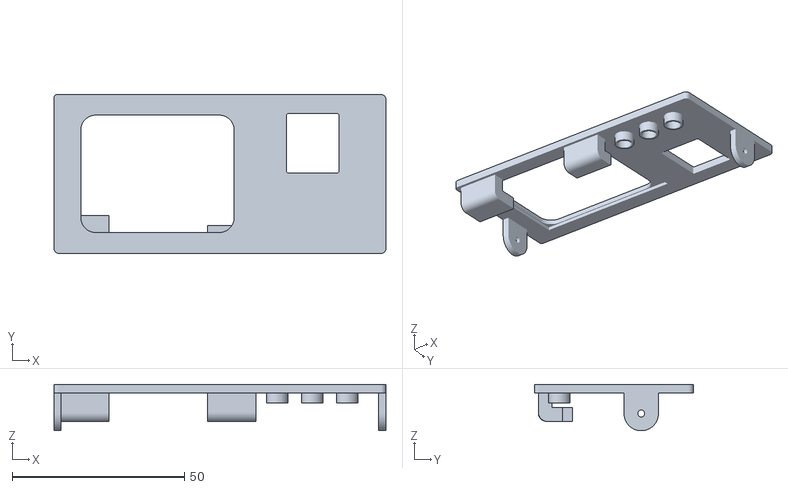
[picture p97: CAD file, 2025-12-18]
resources/3D Models/TRHV4-Hood Front Panel Udrillit.stl
96.4 x 46.2 x 13.5
