jkobler/tricorder-GUI/resources/3D Models/Tricorder Test Stands.FCStd

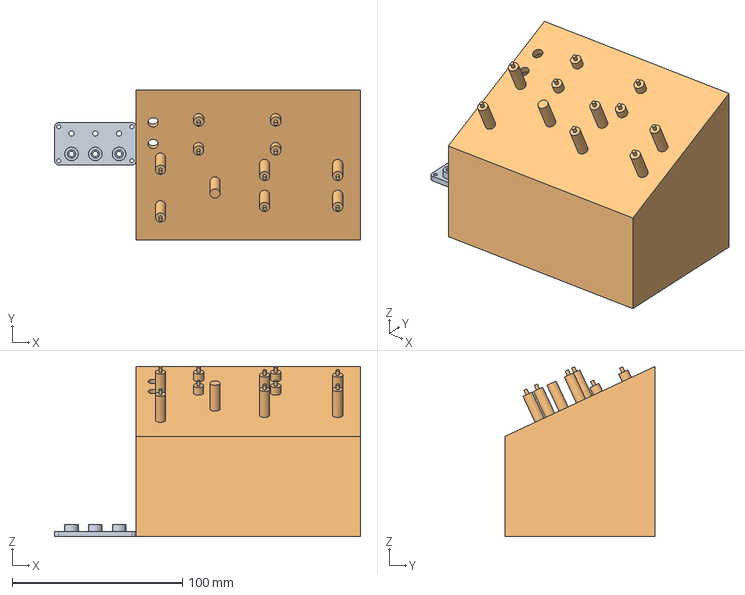
[picture p99: CAD file, 2025-12-18]
resources/3D Models/Tricorder Test Stands.FCStd
180.0 x 88.0 x 100.0 mm
Hood buttons and LEDs
Hood Test Stand
