jkobler/tricorder-GUI/resources/3D Models/Tricorder Test Stands-Hood Test Stand.stl

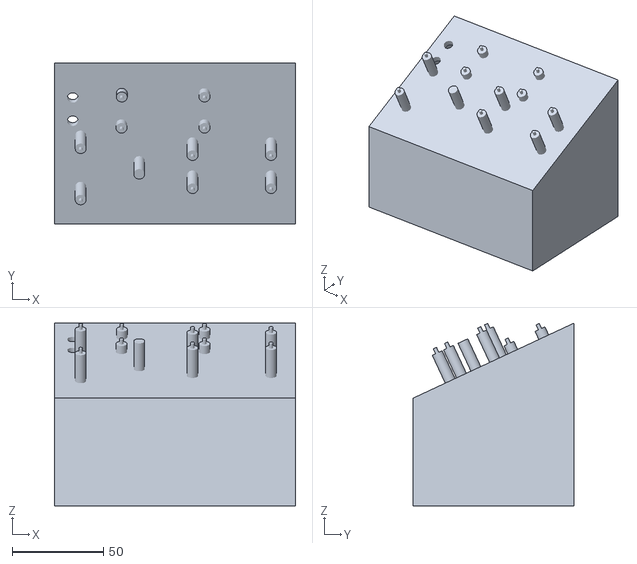
[picture p100: CAD file, 2025-12-18]
resources/3D Models/Tricorder Test Stands-Hood Test Stand.stl
132.0 x 88.0 x 100.0
