jkobler/tricorder-GUI/resources/3D Models/TRHV4-Button Surround.stl

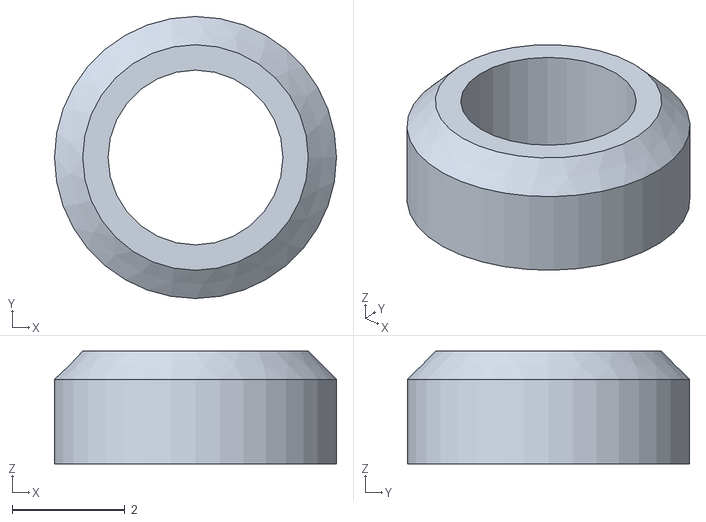
[picture p101: CAD file, 2025-12-18]
resources/3D Models/TRHV4-Button Surround.stl
5.00 x 5.00 x 2.00
