jkobler/tricorder-GUI/resources/3D Models/01. TOS Tricorder(Empty)-STL Files/TTA1-Left Side Frame.3mf

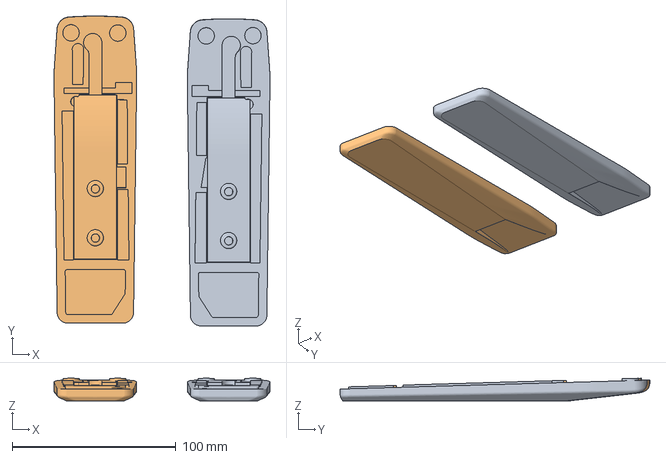
[picture p102: CAD file, 2025-12-18]
resources/3D Models/01. TOS Tricorder(Empty)-STL Files/TTA1-Left Side Frame.3mf
131.8 x 189.0 x 13.8 mm
TTA1-Left Side Panel.stl
TTA1-Right Side Panel.stl
