jkobler/tricorder-GUI/resources/3D Models/TRHV4-Hood Mic Bezel.stl

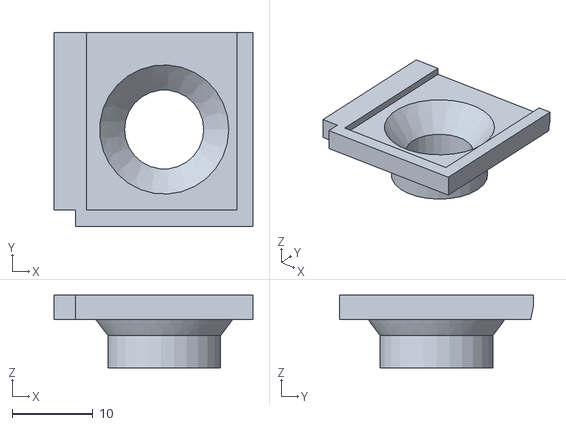
[picture p103: CAD file, 2025-12-18]
resources/3D Models/TRHV4-Hood Mic Bezel.stl
24.6 x 24.0 x 9.00
