jkobler/tricorder-GUI/resources/3D Models/01. TOS Tricorder(Empty)-STL Files/TTA1-Doors and panels.3mf

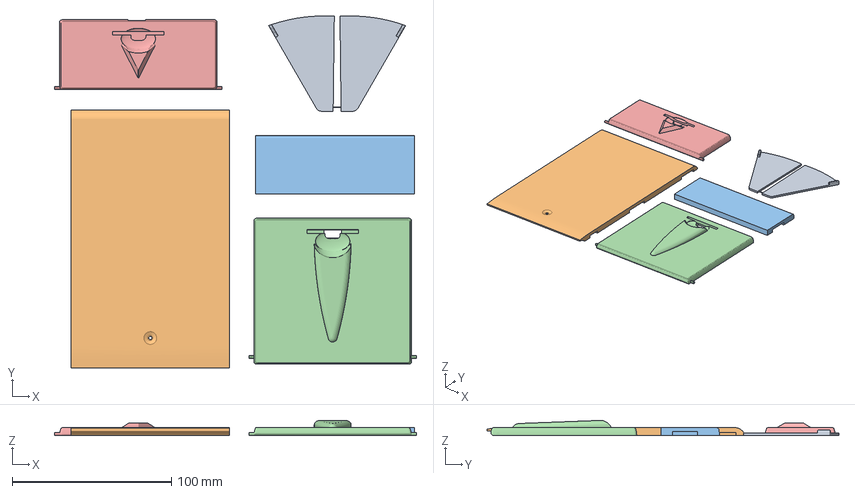
[picture p104: CAD file, 2025-12-18]
resources/3D Models/01. TOS Tricorder(Empty)-STL Files/TTA1-Doors and panels.3mf
227.5 x 221.2 x 9.59 mm
TTA1-Door Catches.stl
TTA1-Back (with screw hole).stl
TTA1-Base.stl
TTA1-Lower Door (Handle B) (with magnet slot).stl
TTA1-Upper Door (Handle B) (with magnet slot).stl
