jkobler/tricorder-GUI/resources/3D Models/Tricorder Frame.FCStd

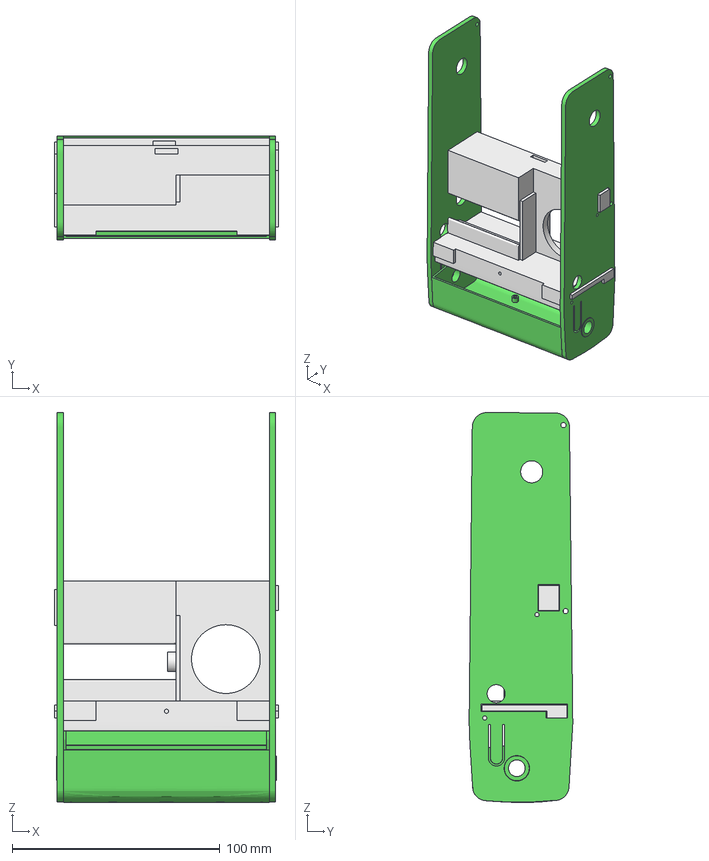
[picture p105: CAD file, 2025-12-18]
resources/3D Models/Tricorder Frame.FCStd
108.0 x 49.9 x 187.7 mm
indent cut 007
Hood
Left Frame Billet
Right Frame Billet
indent cut 008
TTA1-Internal Frame (with magnet slots)
