jkobler/tricorder-GUI/resources/3D Models/01. TOS Tricorder(Empty)-STL Files/TT-Science Scanner 3.stl

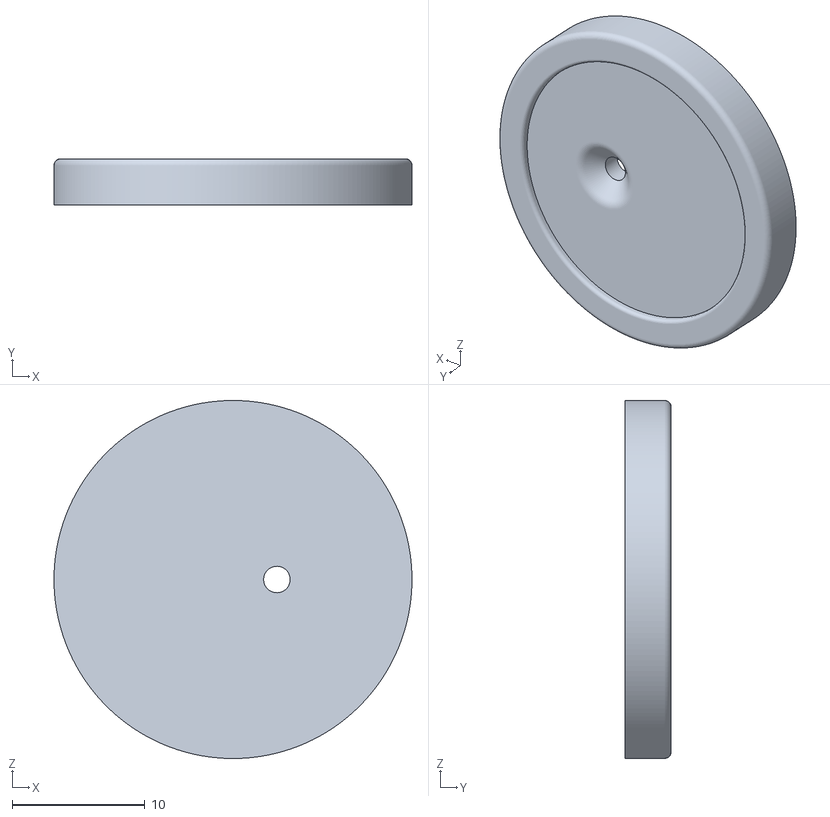
[picture p106: CAD file, 2025-12-18]
resources/3D Models/01. TOS Tricorder(Empty)-STL Files/TT-Science Scanner 3.stl
27.0 x 3.50 x 27.0
