jkobler/tricorder-GUI/resources/3D Models/01. TOS Tricorder(Empty)-STL Files/TTA1-Disc Cylinder.stl

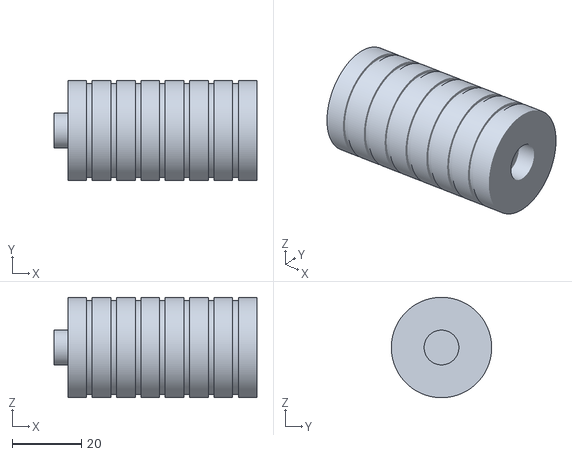
[picture p107: CAD file, 2025-12-18]
resources/3D Models/01. TOS Tricorder(Empty)-STL Files/TTA1-Disc Cylinder.stl
58.5 x 28.9 x 28.9
