jkobler/tricorder-GUI/resources/3D Models/Internal components fit.FCStd

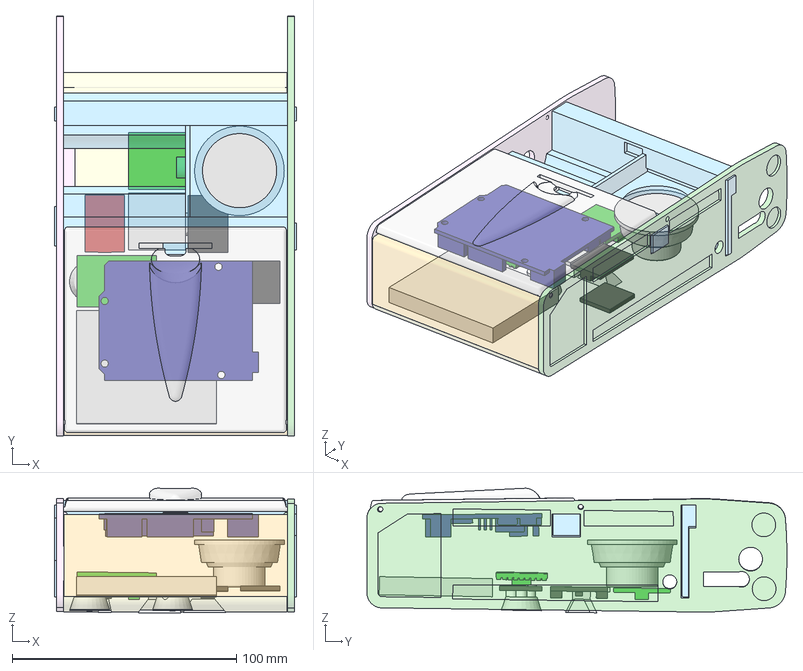
[picture p108: CAD file, 2025-11-17]
resources/3D Models/Internal components fit.FCStd
108.0 x 187.3 x 55.6 mm
bme680 board mockup
Lipoly 3.7v 2500mAh Battery
40mm Speaker
AMG8833 IR Grideye Mockup
Adafruit QT Rotary Encoder BO Mockup
Adafruit VCNL4200 Long Distance IR Proximity and Light Sensor
AMG8833 IR Cutout for Back
VCNL4200 Cutout for Back001
AMG8833 IR Cutout for Back001
ov5640 camera cutout
ov5640 Camera 72d Mockup001
Adafruit PAM8302 Mono Amp MU
LED Cutout
Adafruit Metro ESP32-S3 Board MU
LED Flashlight
TTA1-Lower Door (Handle B) (with magnet slot)
TTA1-Internal Frame (with magnet slots)
TTA1-Left Side Frame
TTA1-Right Side Frame
TTA1-Back (with screw hole)
TTA1-Base
