jkobler/tricorder-GUI/resources/3D Models/01. TOS Tricorder(Empty)-STL Files/TTA1-Hood and Lens Frame.3mf

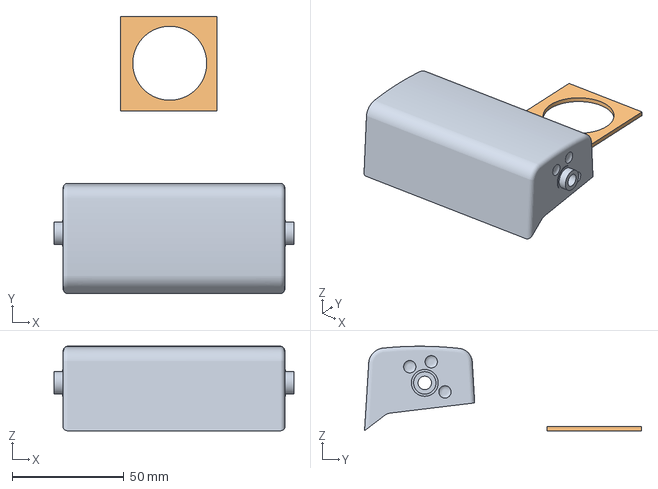
[picture p110: CAD file, 2025-12-18]
resources/3D Models/01. TOS Tricorder(Empty)-STL Files/TTA1-Hood and Lens Frame.3mf
107.2 x 123.9 x 37.9 mm
TTA1-Hood.stl
TTA1-Lens frame panel.stl
