jkobler/tricorder-GUI/resources/3D Models/01. TOS Tricorder(Empty)-STL Files/TTA1-Base.3mf

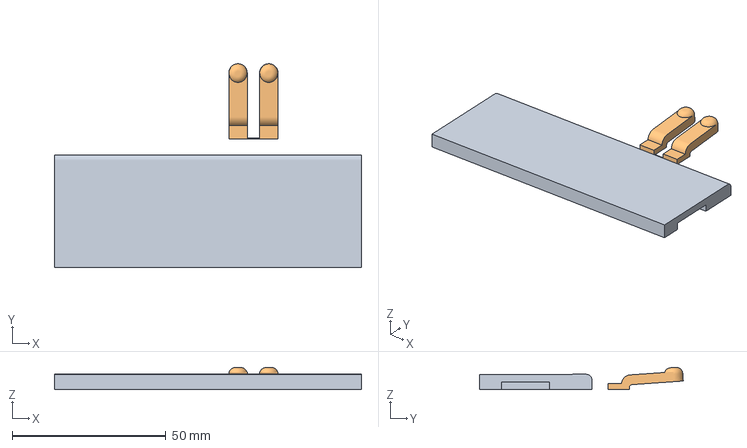
[picture p111: CAD file, 2025-12-18]
resources/3D Models/01. TOS Tricorder(Empty)-STL Files/TTA1-Base.3mf
99.8 x 66.2 x 7.25 mm
TTA1-Base.stl
TTA1-Hood catches.stl
