jkobler/tricorder-GUI/resources/3D Models/01. TOS Tricorder(Empty)-STL Files/TTA1-buttons scanner.3mf

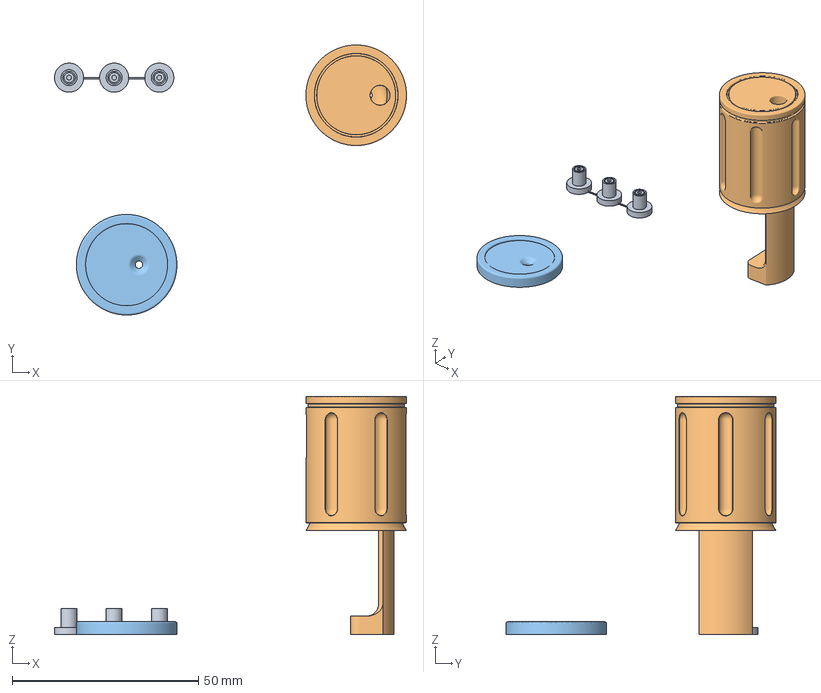
[picture p115: CAD file, 2025-12-18]
resources/3D Models/01. TOS Tricorder(Empty)-STL Files/TTA1-buttons scanner.3mf
94.5 x 72.5 x 64.0 mm
TTA1-Hood buttons.stl
TT-Science Scanner 1.stl
TT-Science Scanner 3.stl
