jkobler/tricorder-GUI/resources/3D Models/01. TOS Tricorder(Empty)-STL Files/TTA1-silver parts, arduino.3mf

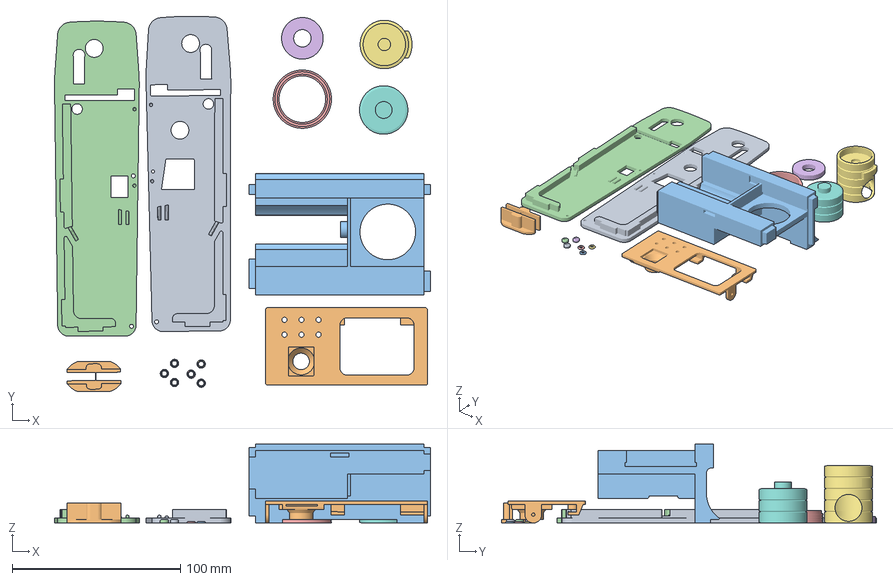
[picture p117: CAD file, 2025-12-18]
resources/3D Models/01. TOS Tricorder(Empty)-STL Files/TTA1-silver parts, arduino.3mf
223.7 x 223.3 x 47.0 mm
TTA1- Left Side Frame.stl
TTA1-Handles B.stl
TTA1-Internal Frame (with magnet slots).stl
TTA1-Left Side Frame.stl
TTA1-Lens Rim.stl
TTA1-Disk Encoder Casing Endcap.stl
TTA1-Disk Encoder Casing.stl
TTA1-Disk Encoder Knob.stl
TRHV4-Button Surround.stl x 3
TRHV4-Hood Front Panel.stl
TRHV4-LED Surround.stl x 3
