jkobler/tricorder-GUI/resources/3D Models/01. TOS Tricorder(Empty)-STL Files/screen alt.FCStd

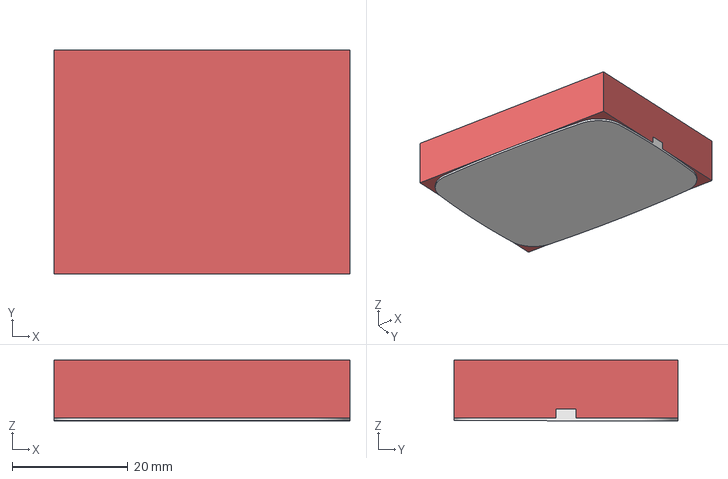
[picture p118: CAD file, 2025-12-18]
resources/3D Models/01. TOS Tricorder(Empty)-STL Files/screen alt.FCStd
51.1 x 38.7 x 10.5 mm
TTA1-Screen
