jkobler/tricorder-GUI/resources/3D Models/01. TOS Tricorder(Empty)-STL Files/TT-Science Scanner 2.stl

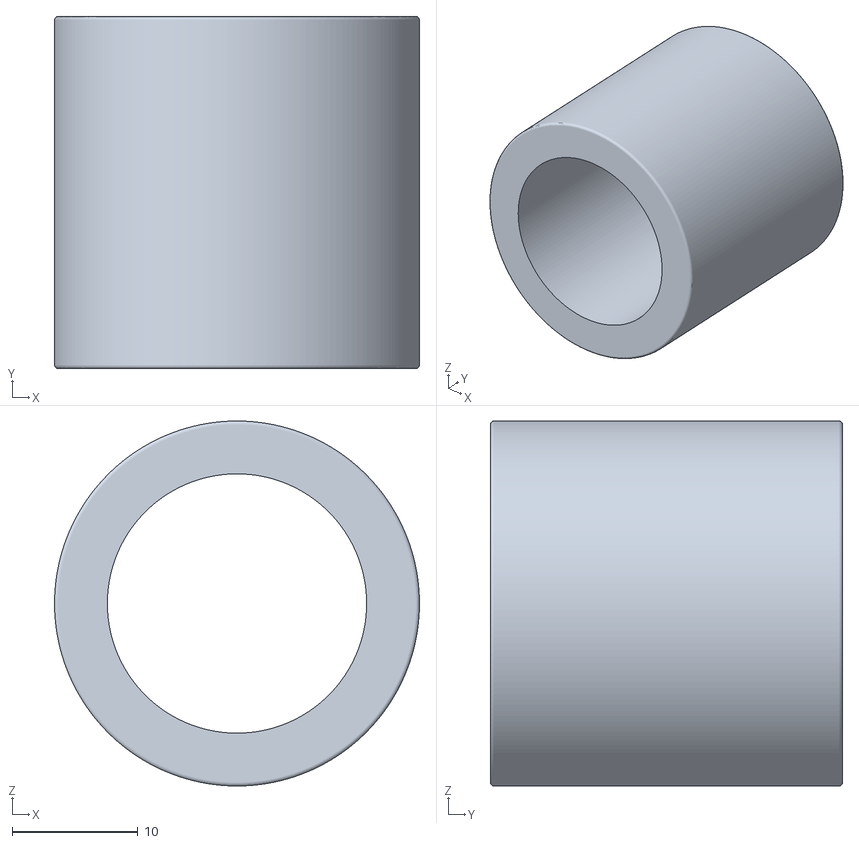
[picture p119: CAD file, 2025-12-18]
resources/3D Models/01. TOS Tricorder(Empty)-STL Files/TT-Science Scanner 2.stl
29.0 x 28.0 x 29.0
