jkobler/tricorder-GUI/resources/3D Models/01. TOS Tricorder(Empty)-STL Files/TTA1-Hood Facia Plate (with false LEDs).stl

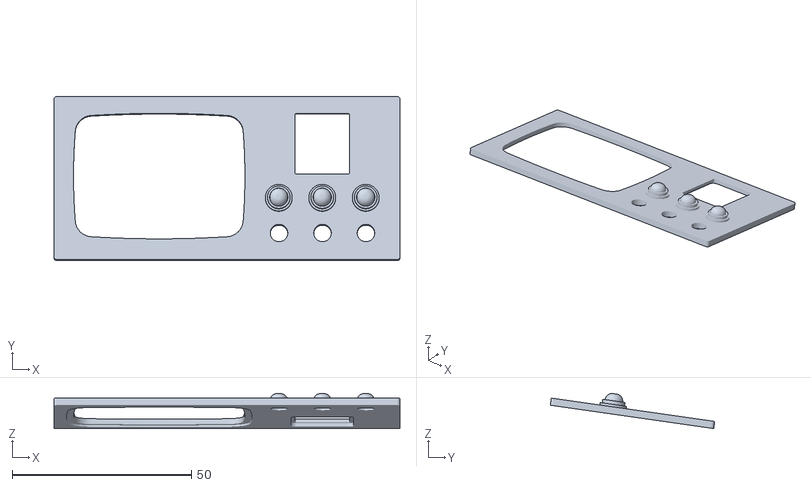
[picture p120: CAD file, 2025-12-18]
resources/3D Models/01. TOS Tricorder(Empty)-STL Files/TTA1-Hood Facia Plate (with false LEDs).stl
96.4 x 45.8 x 9.78
