jkobler/tricorder-GUI/resources/3D Models/01. TOS Tricorder(Empty)-STL Files/TTA1-Side Panels.3mf

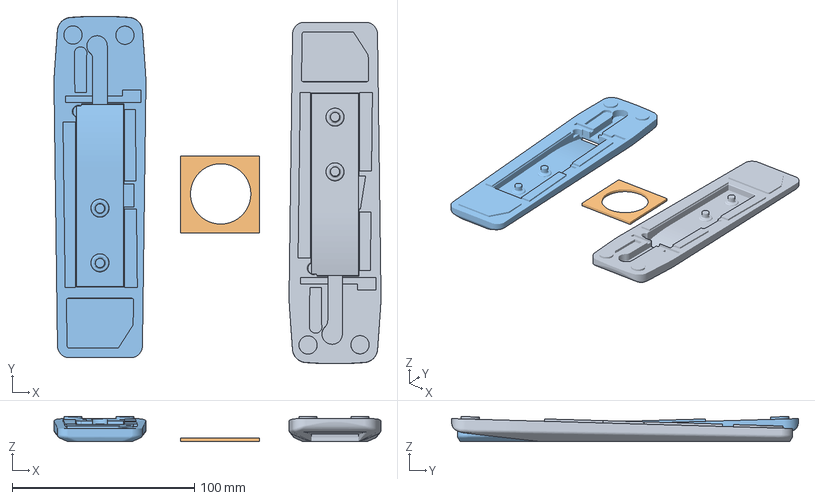
[picture p123: CAD file, 2025-12-18]
resources/3D Models/01. TOS Tricorder(Empty)-STL Files/TTA1-Side Panels.3mf
179.4 x 190.6 x 13.8 mm
TTA1-Left Side Panel.stl
TTA1-Lens frame panel.stl
TTA1-Right Side Panel.stl
