jkobler/tricorder-GUI/resources/3D Models/01. TOS Tricorder(Empty)-STL Files/1 - IMAGES printout.jpg

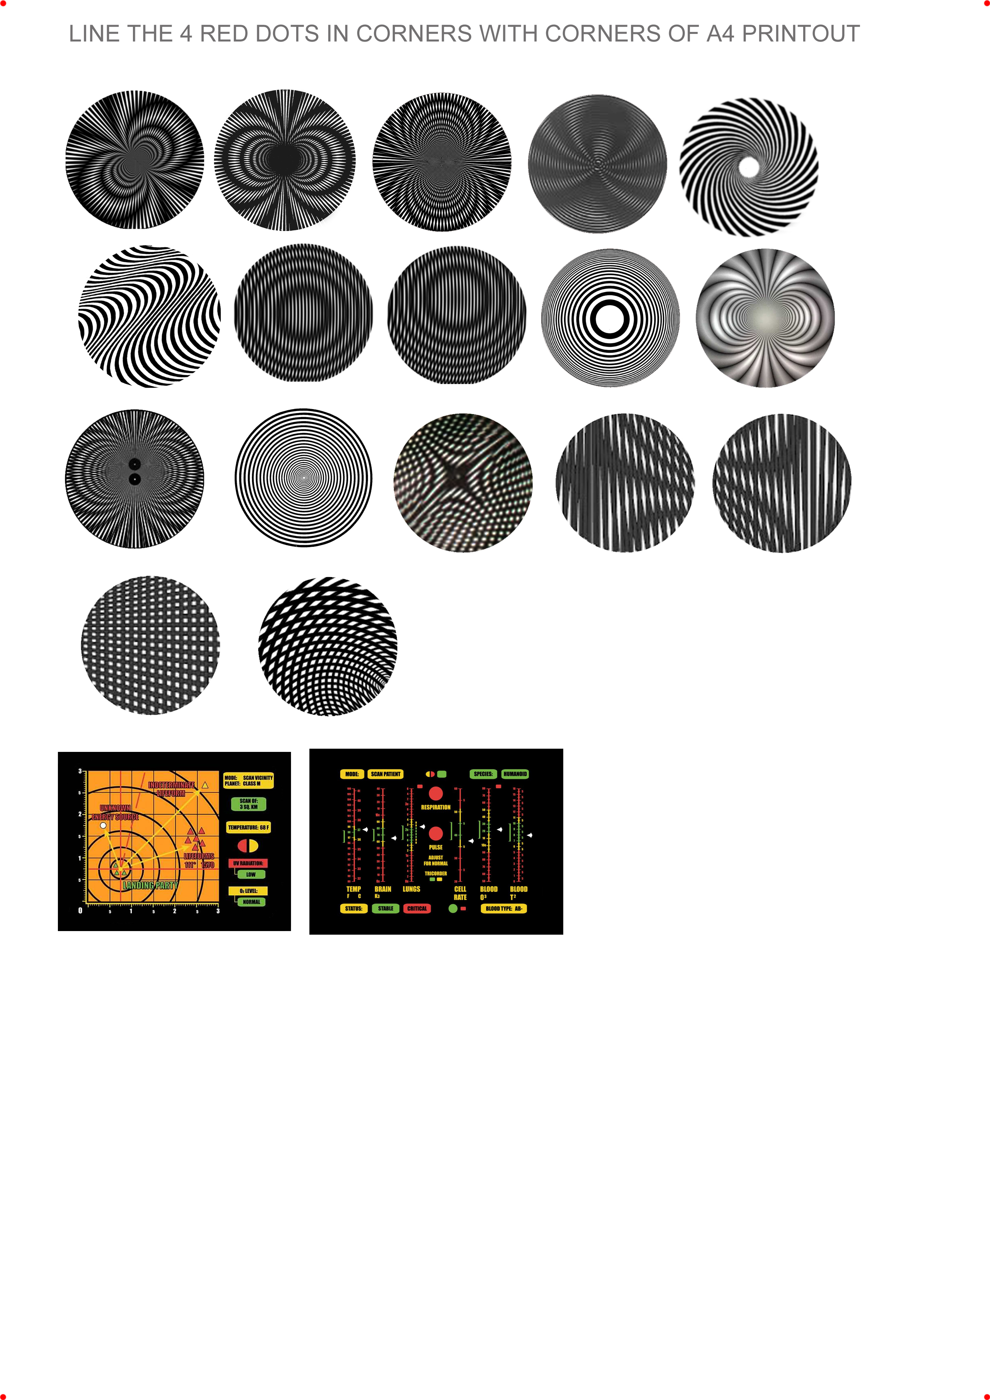
resources/3D Models/01. TOS Tricorder(Empty)-STL Files/1 - IMAGES printout.jpg
