jkobler/tricorder-GUI/resources/images/20251219a-Tricorder Wiring Hood.JPG

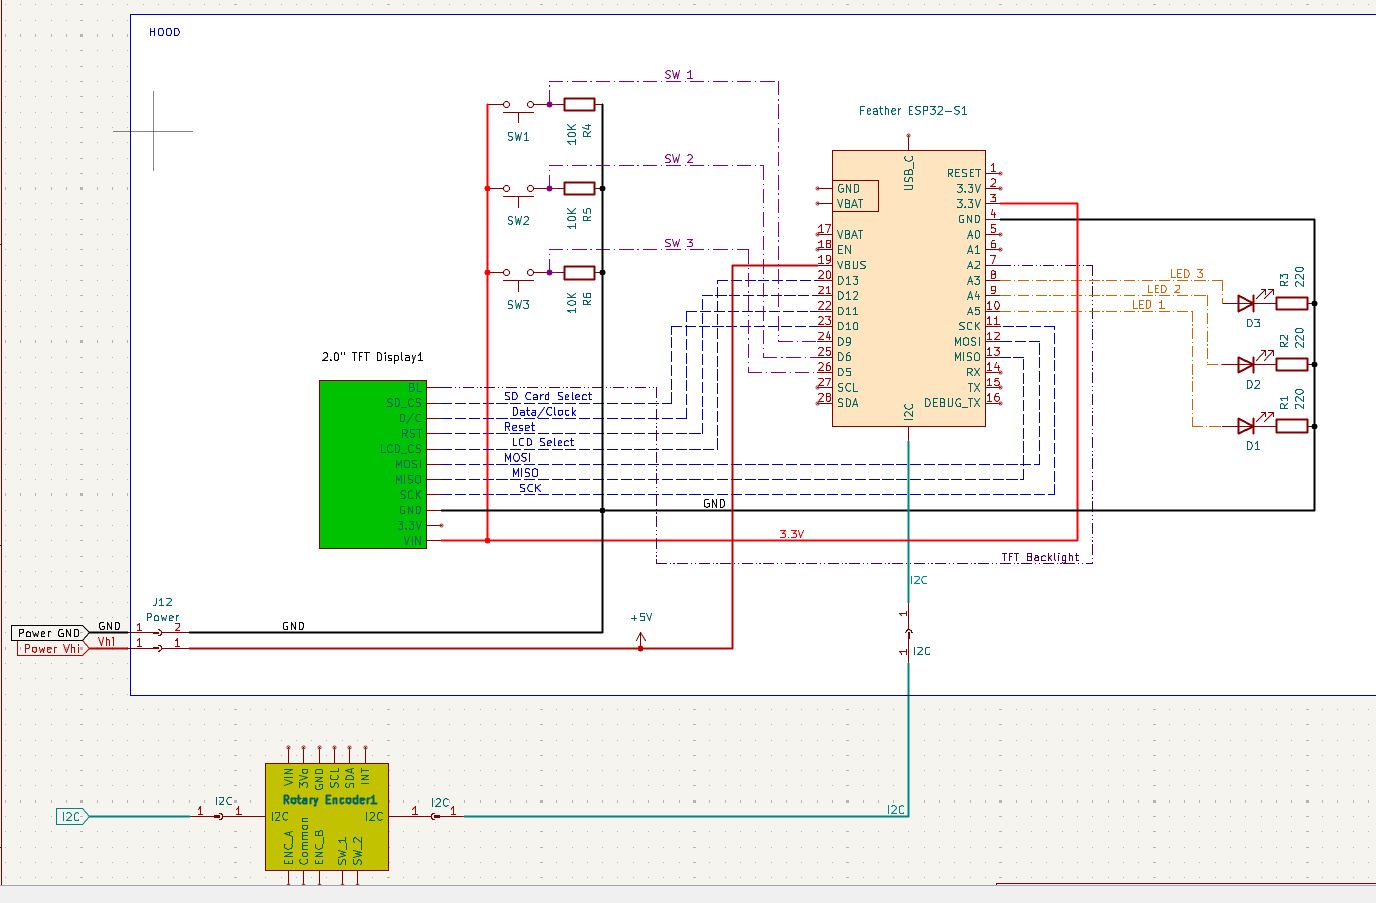
resources/images/20251219a-Tricorder Wiring Hood.JPG
