jkobler/tricorder-GUI/resources/Tricorder Wiring/Hood Wiring Harness.kicad_sch

## KiCad design resources/Tricorder Wiring/Hood Wiring Harness.kicad_sch (2025-12-30)

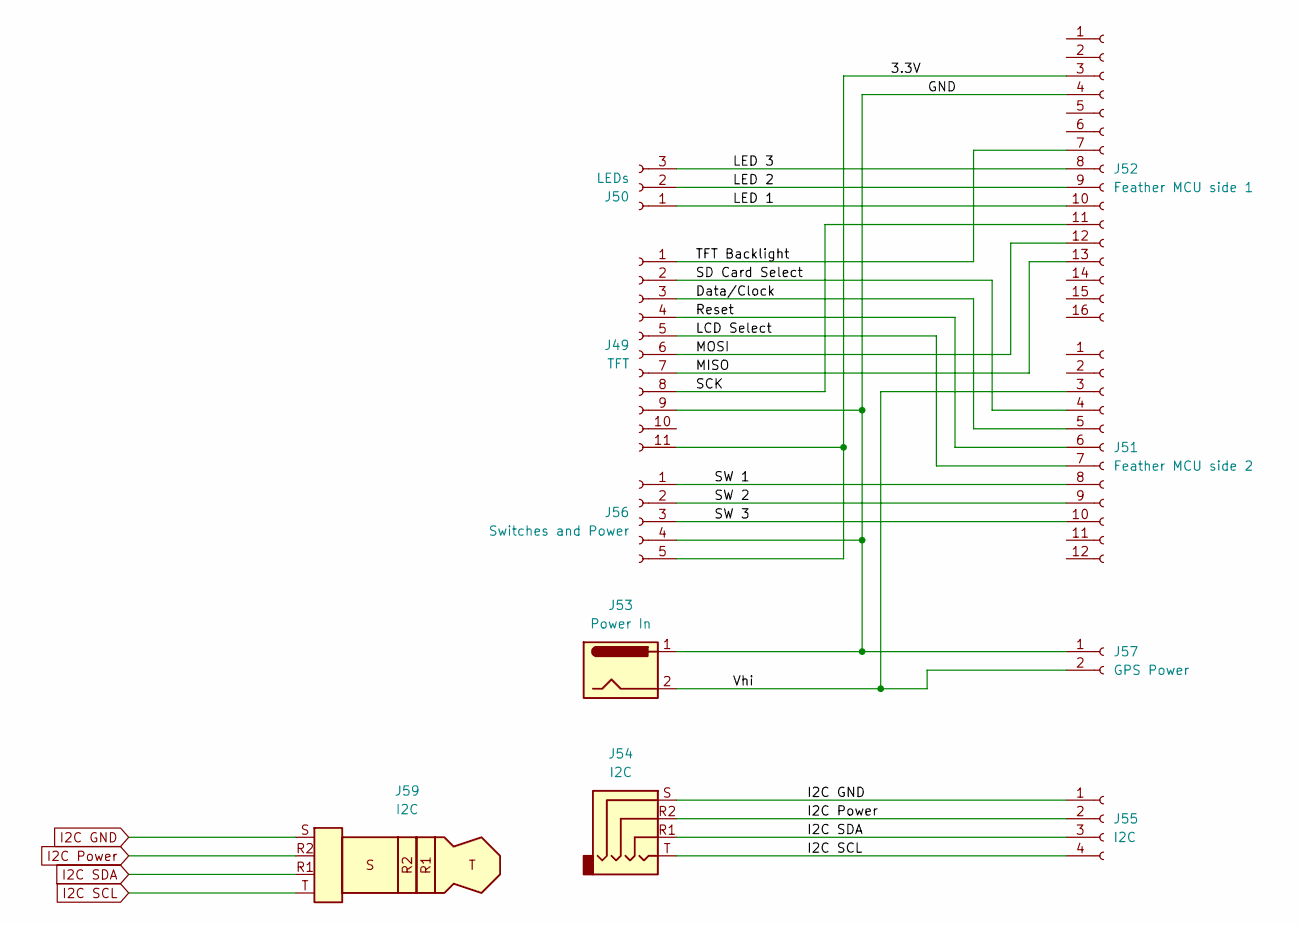
[picture p127: schematic Hood Wiring Harness.kicad_sch]

Parts:
J49: TFT
J50: LEDs
J51: Feather MCU side 2
J52: Feather MCU side 1
J53: Power In
J54, J55, J59: I2C
J56: Switches and Power
J57: GPS Power

Connections:
3.3V: J49.11, J52.3, J56.5
Data/Clock: J49.3, J51.5
GND: J49.9, J52.4, J53.1, J56.4, J57.1
I2C GND: J54.S, J55.1, J59.S
I2C Power: J54.R2, J55.2, J59.R2
I2C SCL: J54.T, J55.4, J59.T
I2C SDA: J54.R1, J55.3, J59.R1
LCD Select: J49.5, J51.7
LED 1: J50.1, J52.10
LED 2: J50.2, J52.9
LED 3: J50.3, J52.8
MISO: J49.7, J52.13
MOSI: J49.6, J52.12
Reset: J49.4, J51.6
SCK: J49.8, J52.11
SD Card Select: J49.2, J51.4
SW 1: J51.8, J56.1
SW 2: J51.9, J56.2
SW 3: J51.10, J56.3
TFT Backlight: J49.1, J52.7
Vhi: J51.3, J53.2, J57.2
