jkobler/tricorder-GUI/resources/Tricorder Wiring/Tricorder Body (ESP32-S3).kicad_sch

## KiCad design resources/Tricorder Wiring/Tricorder Body (ESP32-S3).kicad_sch (2025-12-30)

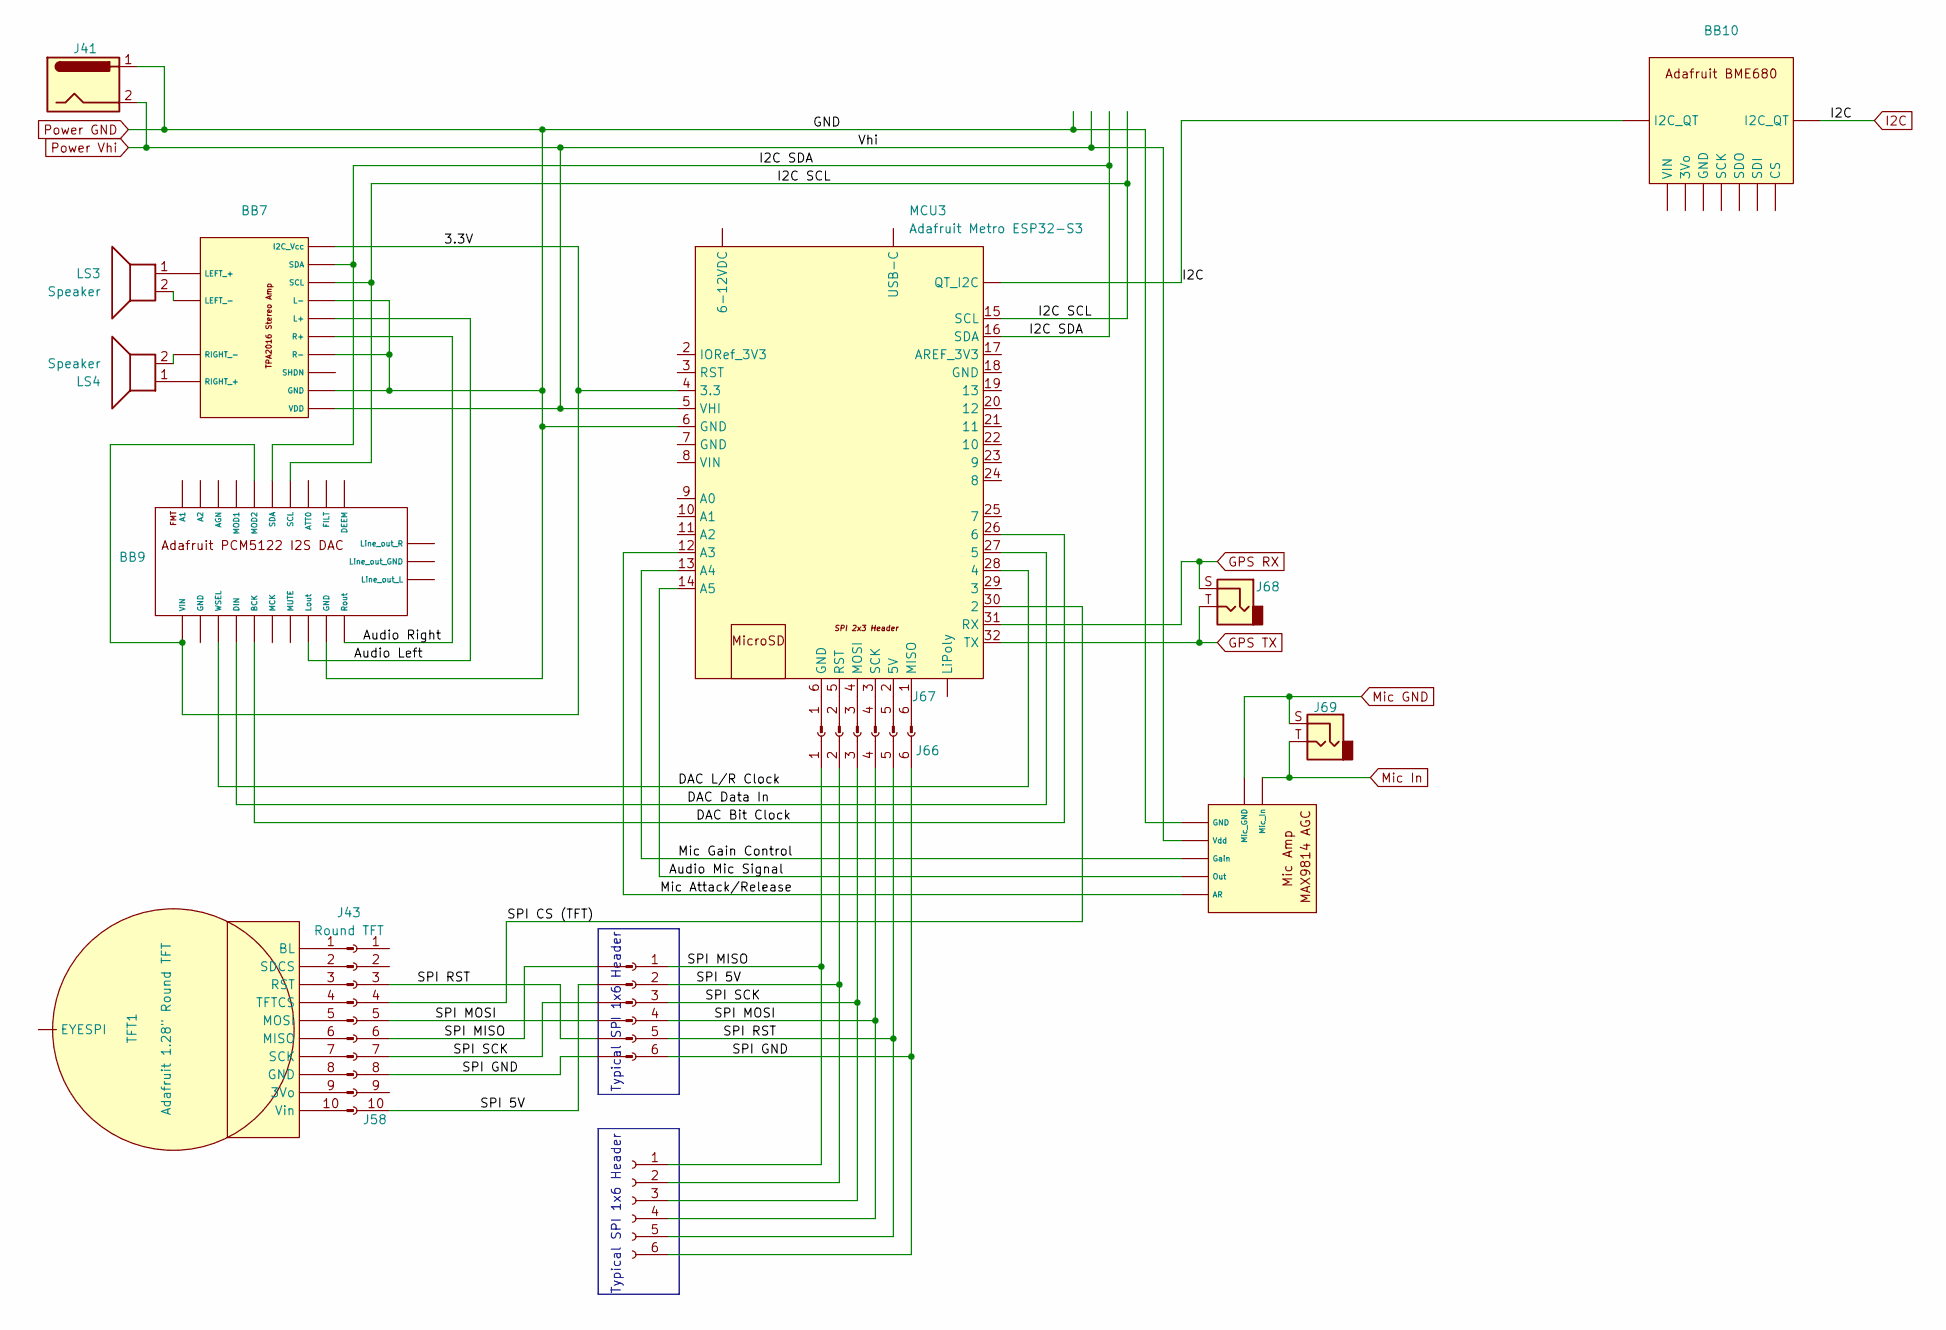
[picture p128: schematic Tricorder Body (ESP32-S3).kicad_sch]

Parts:
BB7, BB9, BB10, BB11: (no value)
J41: Jack-DC
J42, J44, J45, J46, J47, J48: Conn_01x01_Pin
J43: Round TFT
J58: Conn_01x10_Socket
J60, J65: Conn_01x06_Socket
J66, J67: (no value)
J68, J69: AudioJack2
LS3, LS4: Speaker
MCU3: Adafruit Metro ESP32-S3
TFT1: Adafruit 1.28" Round TFT

Connections:
3.3V: BB7., BB9., MCU3.4 (3.3)
Audio Left: BB7., BB9.
Audio Mic Signal: BB11., MCU3.14 (A5)
Audio Right: BB7., BB9.
DAC Bit Clock: BB9., MCU3.26 (6)
DAC Data In: BB9., MCU3.27 (5)
DAC L/R Clock: BB9., MCU3.28 (4)
GPS RX: J68.S, MCU3.31 (RX)
GPS TX: J68.T, MCU3.32 (TX)
I2C: BB10., MCU3. (6-12VDC)
I2C SCL: BB7., BB9., MCU3.15 (SCL)
I2C SDA: BB7., BB9., MCU3.16 (SDA)
Mic Attack/Release: BB11., MCU3.12 (A3)
Mic GND: BB11., J69.S
Mic Gain Control: BB11., MCU3.13 (A4)
Mic In: BB11., J69.T
unnamed: BB7., LS3.1, LS3.2, LS4.1, LS4.2
unnamed: J43.1, TFT1.
unnamed: J43.2, TFT1.
unnamed: J43.3, TFT1.
unnamed: J43.4, TFT1.
unnamed: J43.5, TFT1.
unnamed: J43.6, TFT1.
unnamed: J43.7, TFT1.
unnamed: J43.8, TFT1.
unnamed: J43.9, TFT1.
unnamed: J43.10, TFT1.
unnamed: J67.1, MCU3.6 (GND)
unnamed: J67.2, MCU3.5 (VHI)
unnamed: J67.3, MCU3.4 (3.3)
unnamed: J67.4, MCU3.3 (RST)
unnamed: J67.5, MCU3.2 (IORef_3V3)
unnamed: J67.6, MCU3.1 (MISO)
Power GND: BB7., BB9., BB11., J41.1, MCU3.6 (GND)
Power Vhi: BB7., BB11., J41.2, MCU3.5 (VHI)
SPI 5V: J44., J58.10, J60.2, J65.2, J66.2
SPI CS (TFT): J58.4, MCU3.30 (2)
SPI GND: J48., J58.8, J60.6, J65.6, J66.6
SPI MISO: J42., J58.6, J60.1, J65.1, J66.1
SPI MOSI: J46., J58.5, J60.4, J65.4, J66.4
SPI RST: J47., J58.3, J60.5, J65.5, J66.5
SPI SCK: J45., J58.7, J60.3, J65.3, J66.3

Notes on the sheet:
Typical SPI 1x6 Header
