jkobler/tricorder-GUI/resources/Tricorder Wiring/Tricorder Wiring.kicad_sch

## KiCad design resources/Tricorder Wiring/Tricorder Wiring.kicad_sch (2025-12-30)

Schematic: Tricorder Wiring.kicad_sch

Parts:
2.0{dblquote} TFT Display1: (no value)
BB2: (no value)
D1, D2, D3: LED
J, J1, J2, J3, J4: I2C
J5, J6, J7: Conn_01x01_Pin
J12: Power
J35: Jack-DC
J37, J38: AudioJack2
MCU2: Feather ESP32-S2
MK1: Microphone
R1, R2, R3: 220
R4, R5, R6: 10K
Rotary Encoder1: (no value)
SW1, SW2, SW3: SW_Push

Connections:
3.3V: 2.0{dblquote} TFT Display1., MCU2.3 (3.3V), SW1.2, SW2.2, SW3.2
+5V: BB2., J12.1, J35.2, MCU2.19 (VBUS)
Data/Clock: 2.0{dblquote} TFT Display1., MCU2.21 (D12)
GPS RX: BB2., J38.S
GPS TX: BB2., J38.T
I2C: J1.1, J2.1, J3.1, J5.1, MCU2. (USB_C)
LCD Select: 2.0{dblquote} TFT Display1., MCU2.23 (D10)
LED 1: D1.2 (A), MCU2.10 (A5)
LED 2: D2.2 (A), MCU2.9 (A4)
LED 3: D3.2 (A), MCU2.8 (A3)
MISO: 2.0{dblquote} TFT Display1., MCU2.13 (MISO)
MOSI: 2.0{dblquote} TFT Display1., MCU2.12 (MOSI)
Mic GND: J37.T, MK1.1 (-)
Mic In: J37.S, MK1.2 (+)
unnamed: D1.1 (K), R1.1
unnamed: D2.1 (K), R2.1
unnamed: D3.1 (K), R3.1
unnamed: J4.1, Rotary Encoder1.
unnamed: J.1, Rotary Encoder1.
Power GND: 2.0{dblquote} TFT Display1., BB2., J6.1, J12.2, J35.1, MCU2.4 (GND), R1.2, R2.2, R3.2, R4.1, R5.1, R6.1
Power Vhi: J7.1
SCK: 2.0{dblquote} TFT Display1., MCU2.11 (SCK)
SD Card Select: 2.0{dblquote} TFT Display1., MCU2.20 (D13)
SPI RST: 2.0{dblquote} TFT Display1., MCU2.22 (D11)
SW 1: MCU2.24 (D9), R4.2, SW1.1
SW 2: MCU2.25 (D6), R5.2, SW2.1
SW 3: MCU2.26 (D5), R6.2, SW3.1
TFT Backlight: 2.0{dblquote} TFT Display1., MCU2.7 (A2)

Notes on the sheet:
HOOD
