jkobler/tricorder-GUI/resources/Tricorder Wiring/tricorder body.kicad_sch

## KiCad design resources/Tricorder Wiring/tricorder body.kicad_sch (2025-12-30)

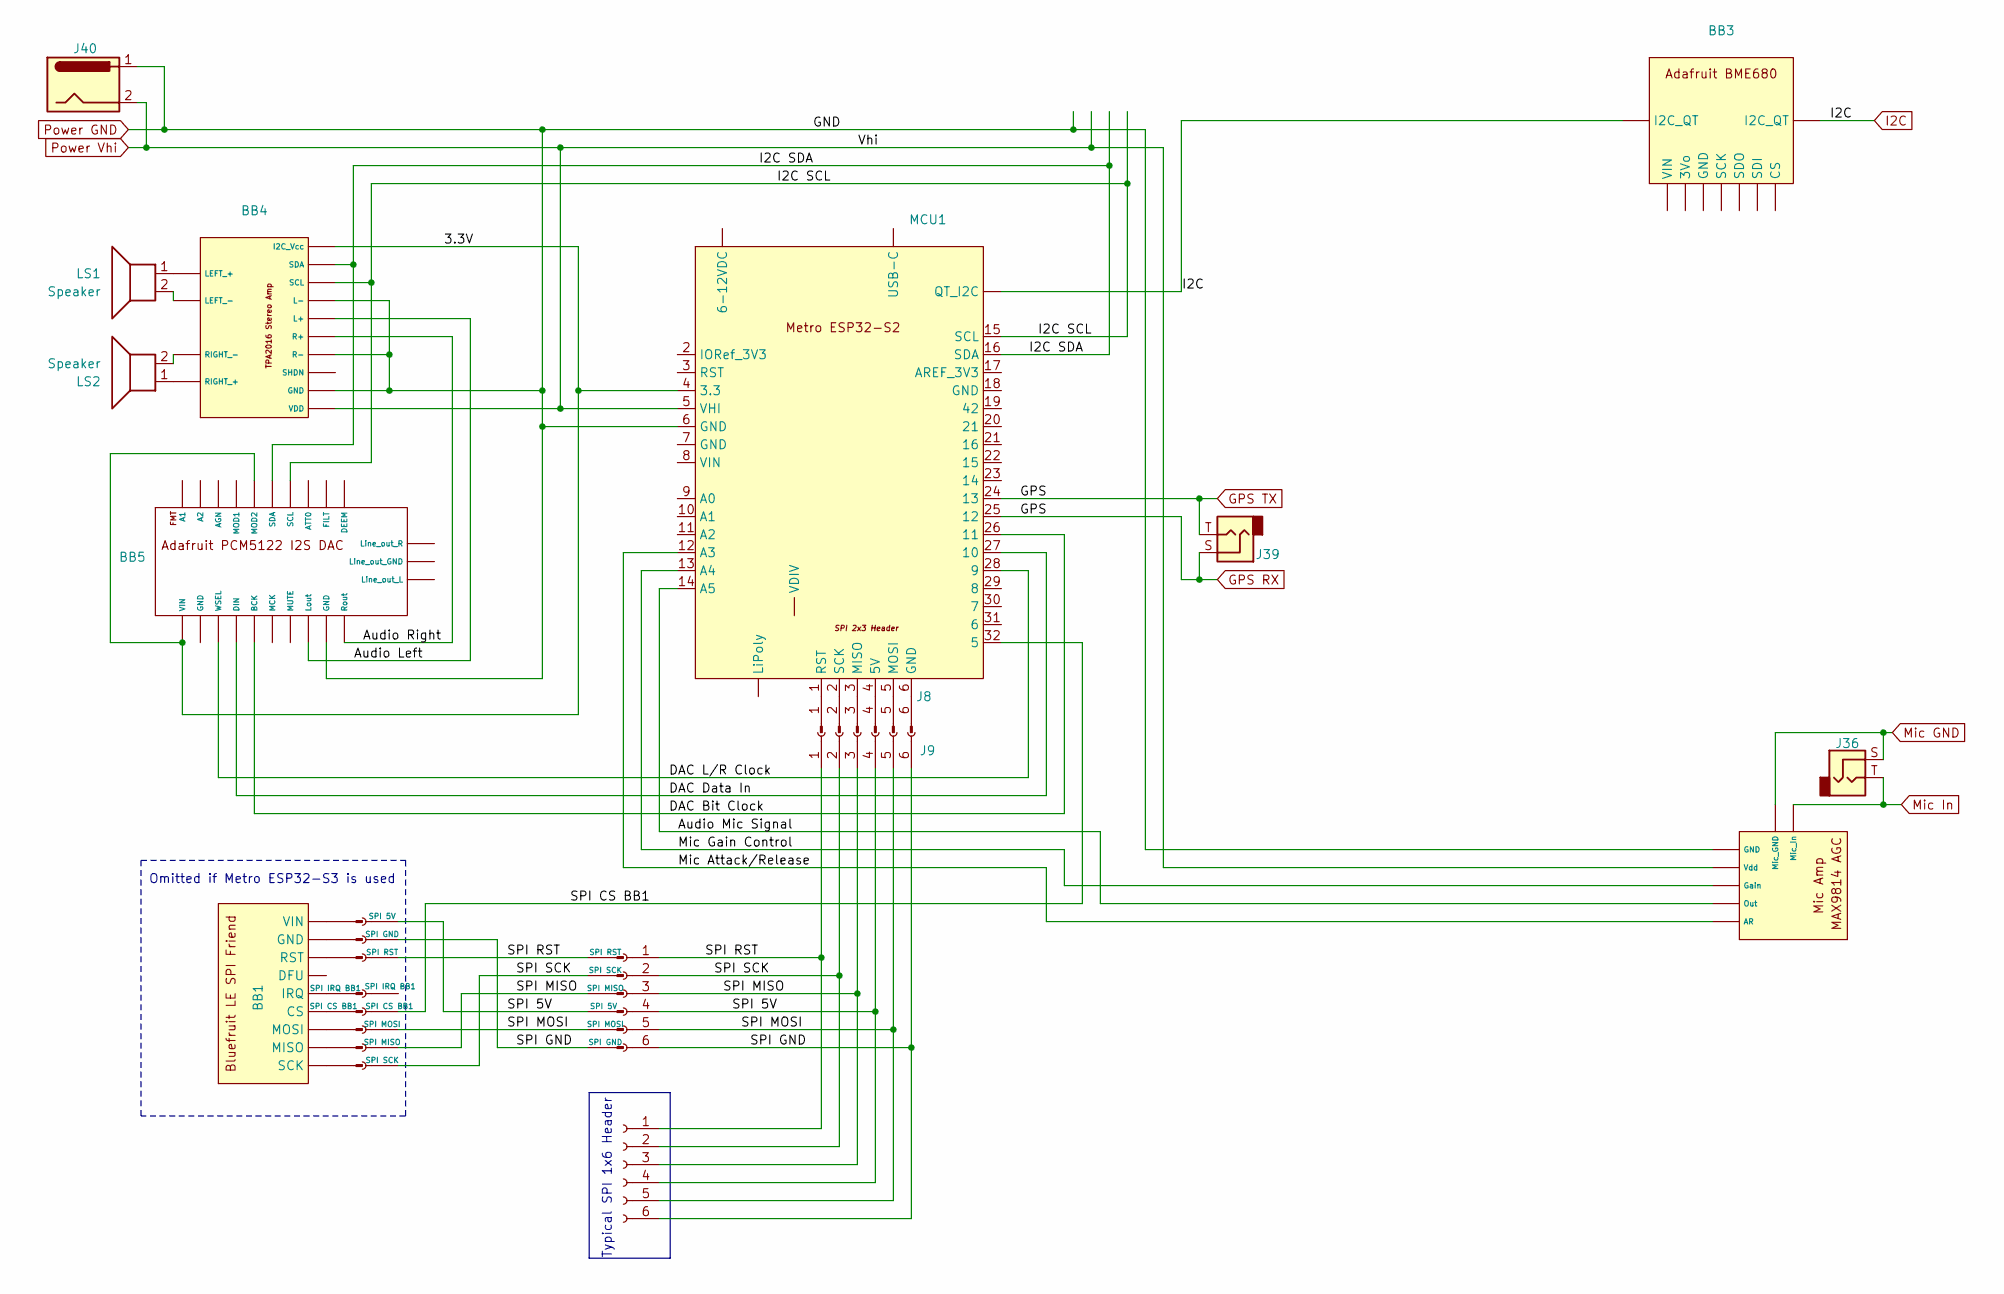
[picture p129: schematic tricorder body.kicad_sch]

Parts:
BB1, BB3, BB4, BB5, BB6: (no value)
J8, J9: (no value)
J10, J30: SPI SCK
J11, J31: SPI RST
J13, J28: SPI MISO
J14, J26: SPI 5V
J15, J29: SPI MOSI
J16, J27: SPI GND
J17, J32: SPI CS BB1
J18, J19, J20, J21, J22, J23: Conn_01x01_Pin
J24, J25: Conn_01x06_Socket
J33, J34: SPI IRQ BB1
J36, J39: AudioJack2
J40: Jack-DC
LS1, LS2: Speaker
MCU1: (no value)

Connections:
3.3V: BB4., BB5., MCU1.4 (3.3)
Audio Left: BB4., BB5.
Audio Mic Signal: BB6., MCU1.14 (A5)
Audio Right: BB4., BB5.
DAC Bit Clock: BB5., MCU1.26 (11)
DAC Data In: BB5., MCU1.27 (10)
DAC L/R Clock: BB5., MCU1.28 (9)
GPS RX: J39.S, J39.T, MCU1.24 (13), MCU1.25 (12)
I2C: BB3., MCU1. (6-12VDC)
I2C SCL: BB4., BB5., MCU1.15 (SCL)
I2C SDA: BB4., BB5., MCU1.16 (SDA)
Mic Attack/Release: BB6., MCU1.12 (A3)
Mic GND: BB6., J36.S
Mic Gain Control: BB6., MCU1.13 (A4)
Mic In: BB6., J36.T
unnamed: BB1., J18., J19., J20., J21., J22., J23., J32., J33.
unnamed: BB4., LS1.1, LS1.2, LS2.1, LS2.2
unnamed: J8.1, MCU1.1 (RST)
unnamed: J8.2, MCU1.2 (IORef_3V3)
unnamed: J8.3, MCU1.3 (RST)
unnamed: J8.4, MCU1.4 (3.3)
unnamed: J8.5, MCU1.5 (VHI)
unnamed: J8.6, MCU1.6 (GND)
Power GND: BB4., BB5., BB6., J40.1, MCU1.6 (GND)
Power Vhi: BB4., BB6., J40.2, MCU1.5 (VHI)
SPI 5V: J9.4, J14., J24.4, J25.4, J26.
SPI CS BB1: J17., MCU1.32 (5)
SPI GND: J9.6, J16., J24.6, J25.6, J27.
SPI MISO: J9.3, J13., J24.3, J25.3, J28.
SPI MOSI: J9.5, J15., J24.5, J25.5, J29.
SPI RST: J9.1, J11., J24.1, J25.1, J31.
SPI SCK: J9.2, J10., J24.2, J25.2, J30.

Notes on the sheet:
Typical SPI 1x6 Header
Omitted if Metro ESP32-S3 is used
